Jadecky/Printer_Mods/Micron/Micron/Display Bezel Border Accent/readme.md

4.3 display bezel with minimal accent around the display border. 

Can be split and printed with an MMU, or a simple filament swap at 1.2mm.

Has built in support for optional accent logo insert.

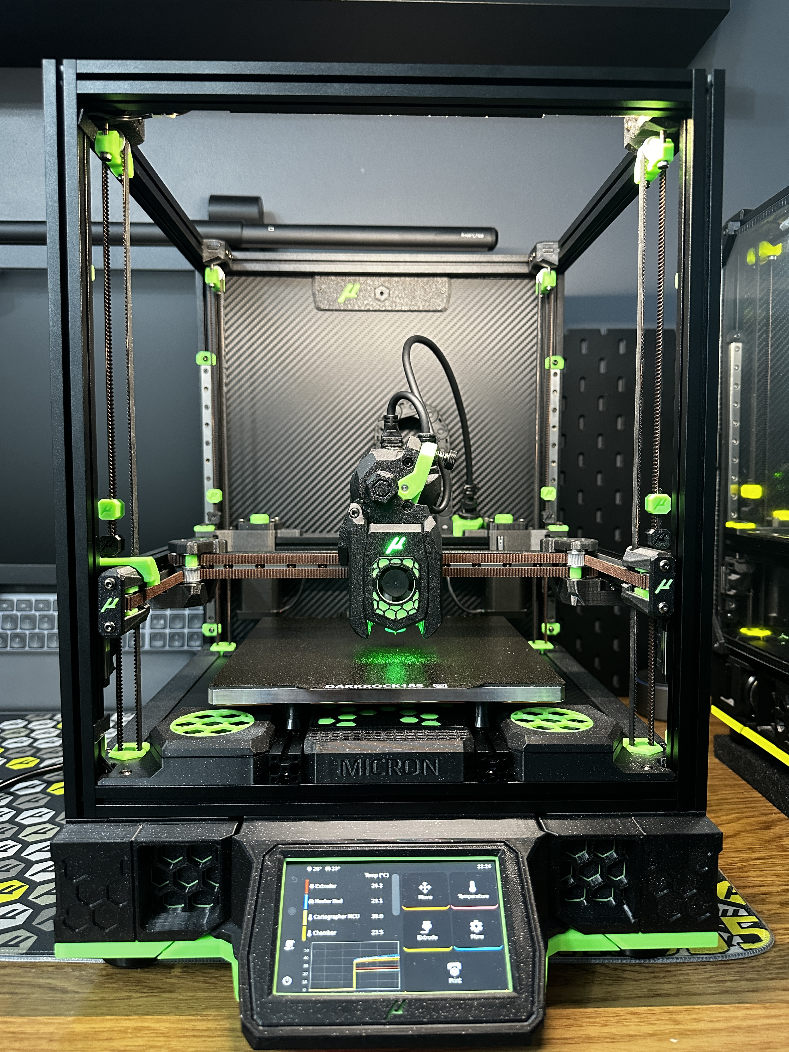
[picture p29: Micron/Micron/Display Bezel Border Accent/Images/Printed.JPG]
Printed


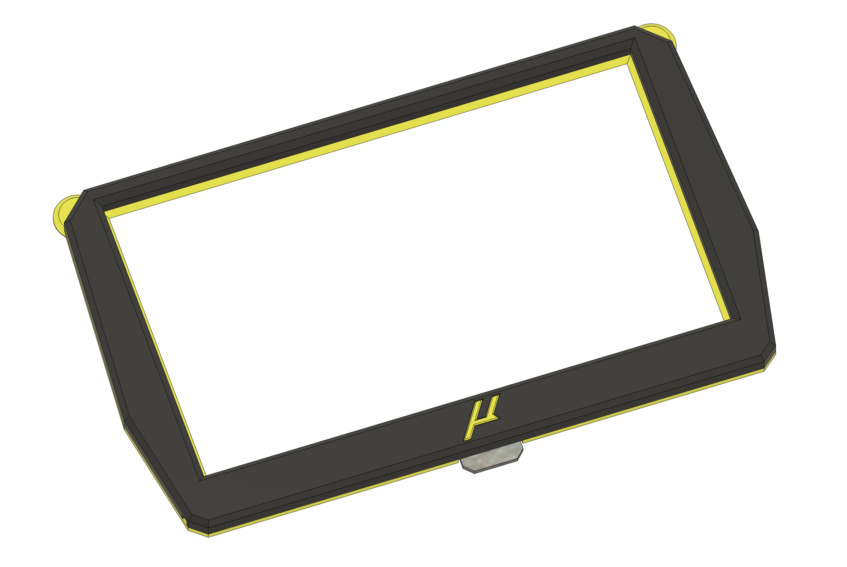
[picture p30: Micron/Micron/Display Bezel Border Accent/Images/CAD.png]
CAD Example
