Jadecky/Printer_Mods/Micron/Micron/R1 Spool Holder_Dual Colour/readme.md

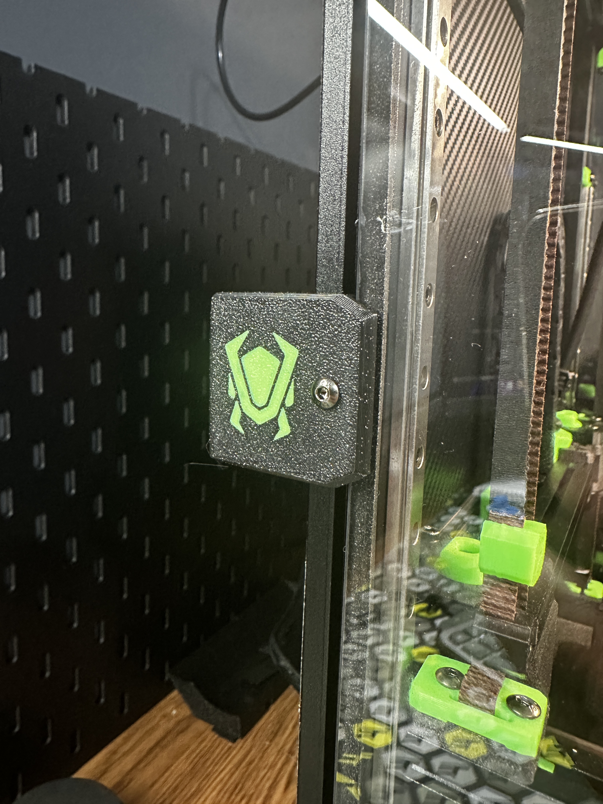
[picture p31: Micron/Micron/R1 Spool Holder_Dual Colour/Images/Printed.JPG]
Printed


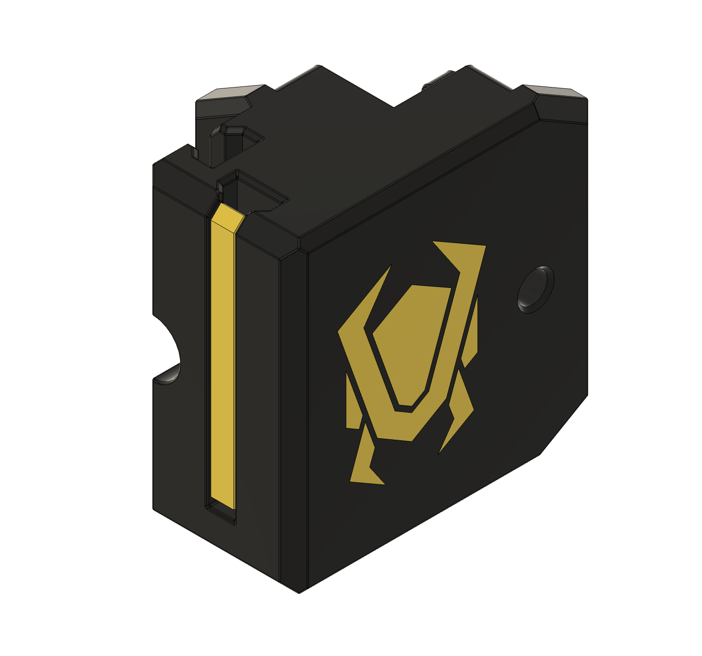
[picture p32: Micron/Micron/R1 Spool Holder_Dual Colour/Images/CAD.png]
CAD Example
