Jadecky/Printer_Mods/Micron/Micron/Stealth Fan Grills/README.md

# Stealth Fan Grills for Micron+

Slight modification to the stock **Micron+ Fan Grills**, reducing the visible accent areas for a more subtle, stealthy look.

Uses an **accent insert** for the logo — make sure you install this *before* heatsetting your grills into place.

Stealth Fan Grill Example
