Jadecky/Printer_Mods/Micron/Micron/ERCF 1515 Mount/readme.md

# ERCF 1515 Mounts for Micron+

Like the roof rack on your car — but for your printer, to carry your MMU goodness.

Designed to mount the ERCF (or other MMU setups) neatly onto the top 1515 extrusions of your Micron+.

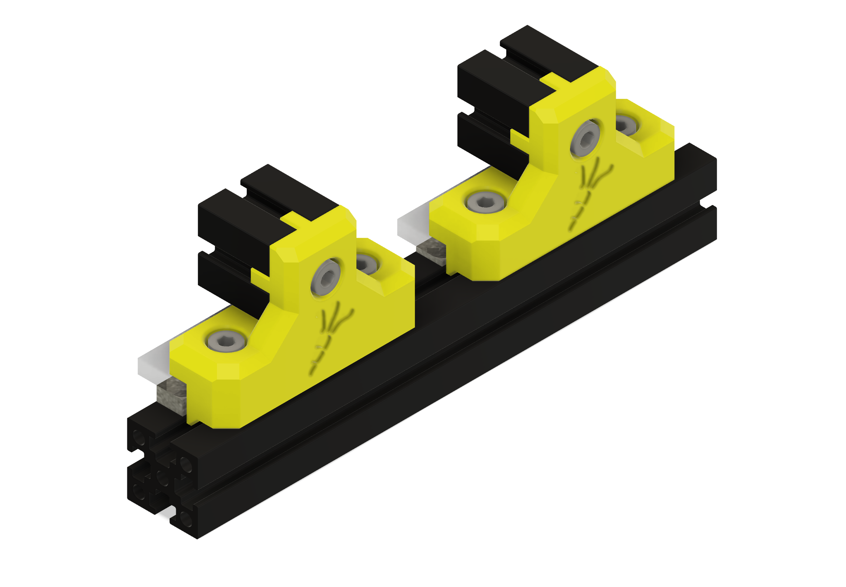
[picture p34: Micron/Micron/ERCF 1515 Mount/Images/ERCF_1515_Mounts.png]
ERCF 1515 Mount Example
