Jadecky/Printer_Mods/Micron/Micron/Micron Bed Stand Off Sleeves/README.md

# Micron Bed Stand Off Sleeves

Micron now uses stand offs to mount the bed, this makes for much easier removal and refitting. 

These standoff sleves just make them a little prettier, especially when paired with a cone washer on the bottom.

---

## 🔗 Suggested Cone / Cap head Washers

| Vendor |
|--------|
|[AliExpress](https://s.click.aliexpress.com/e/_EQEJIOK) |

|[Amazon UK](https://amzn.to/3ZXLOMW) |

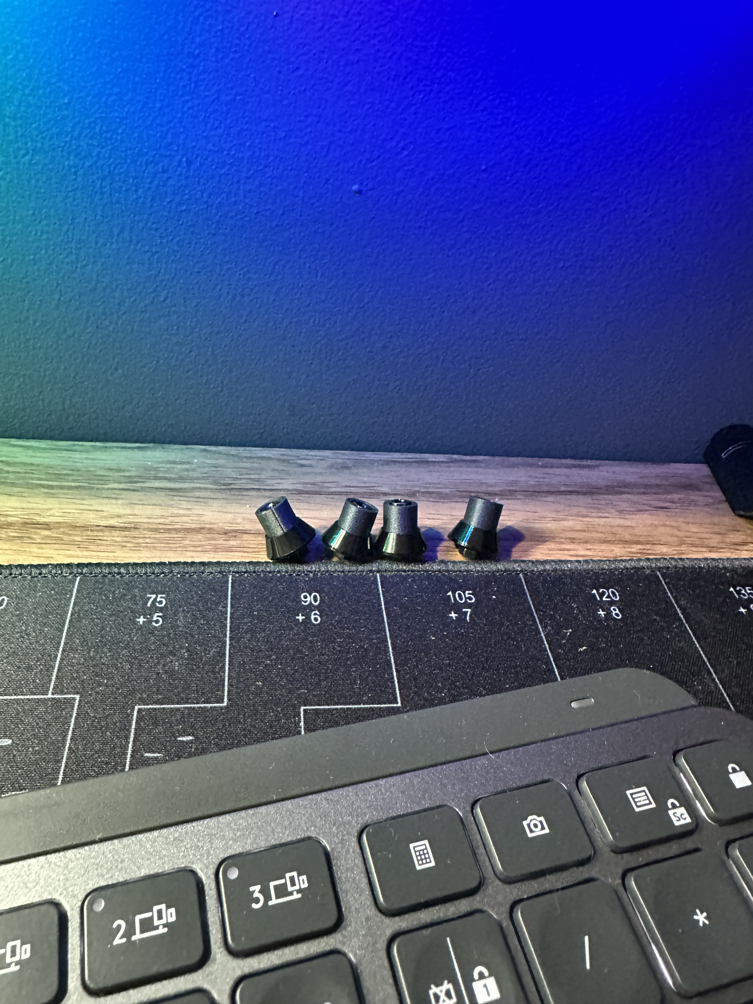
[picture p36: Micron/Micron/Micron Bed Stand Off Sleeves/Images/Standoffs.jpg]
example
