Jadecky/Printer_Mods/Micron+/WAGO_221-415_1515_Mounts/Images/Screenshot 2024-08-23 at 23.59.15.png

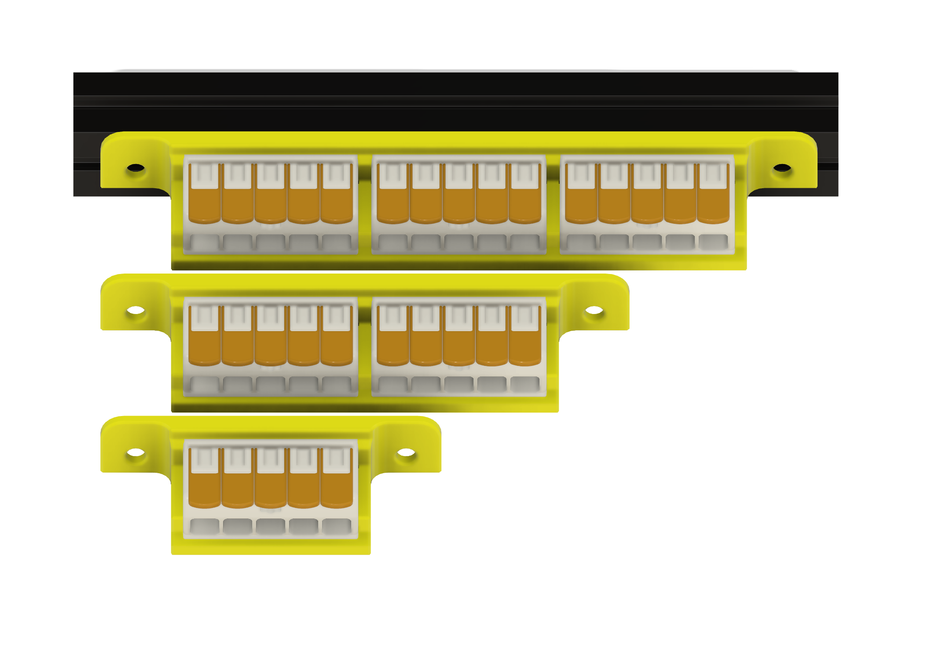
Micron+/WAGO_221-415_1515_Mounts/Images/Screenshot 2024-08-23 at 23.59.15.png
