Jadecky/Printer_Mods/Micron/Micron/AntHead_NH36 Mount/Images/Built_in_support_plug.png

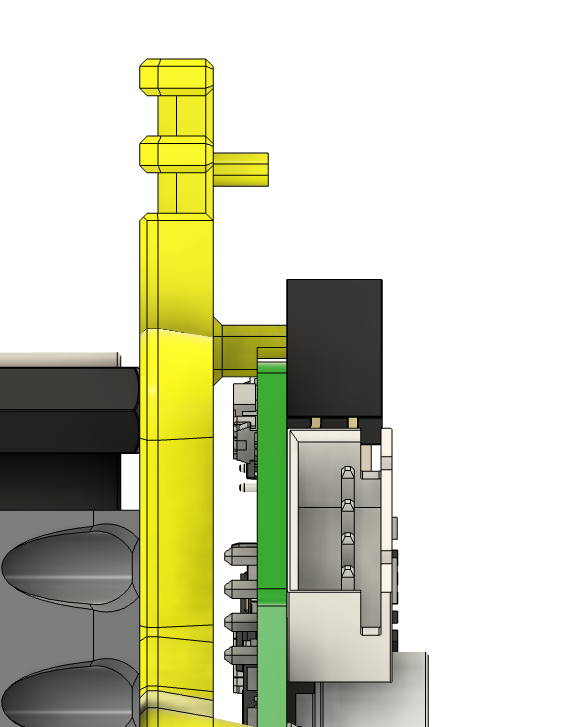
Micron/Micron/AntHead_NH36 Mount/Images/Built_in_support_plug.png
