Jadecky/Printer_Mods/Micron/Micron/Micron Z Belt Clamp/Images/Belt_path.png

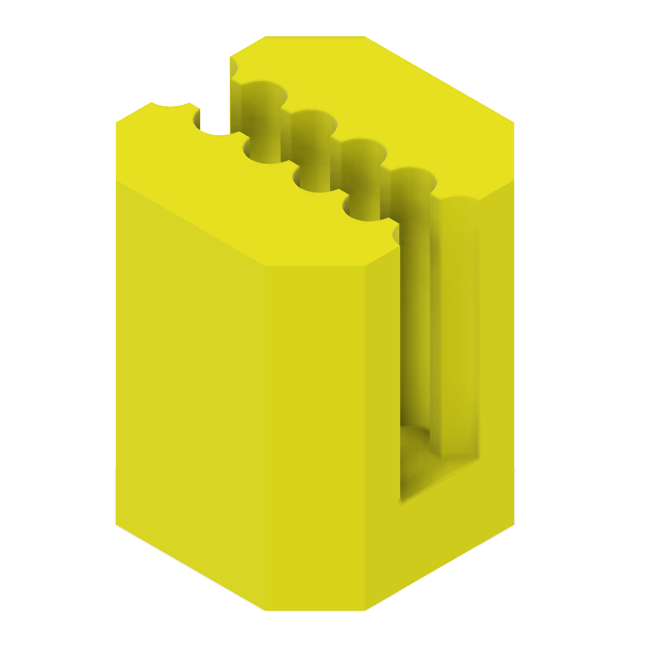
Micron/Micron/Micron Z Belt Clamp/Images/Belt_path.png
