Jadecky/Printer_Mods/Micron/Micron/Micron Z Belt Clamp/Images/IMG_4057.JPG

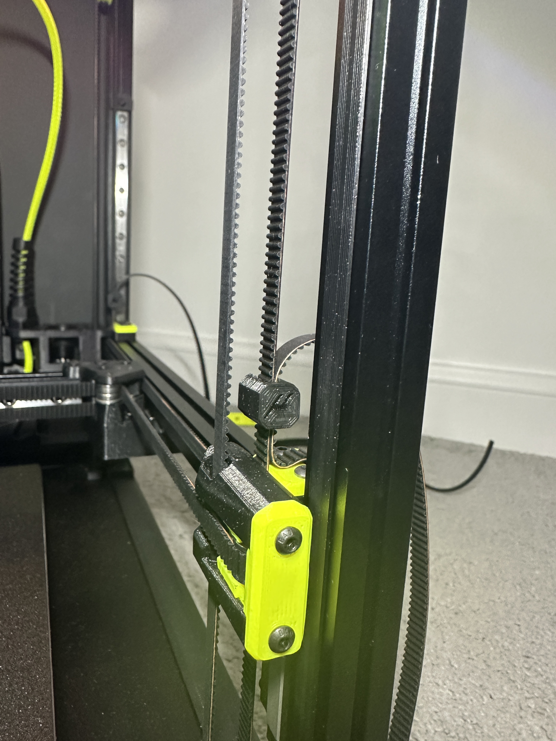
Micron/Micron/Micron Z Belt Clamp/Images/IMG_4057.JPG
