Jadecky/Printer_Mods/Micron+/Z Covers_Cable Access/[a]_Z_Belt_Cover_Cable_b_x2.stl

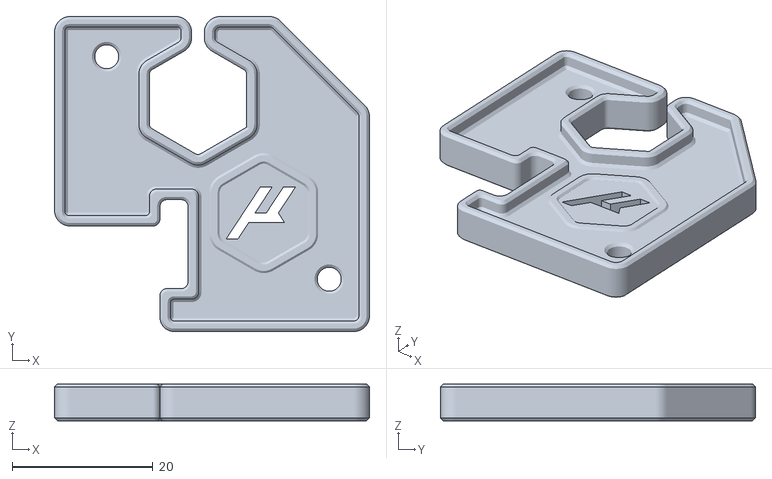
[picture p58: CAD file, 2023-08-23]
Micron+/Z Covers_Cable Access/[a]_Z_Belt_Cover_Cable_b_x2.stl
44.8 x 44.8 x 5.25
