Jadecky/Printer_Mods/Micron+/Z Covers_Cable Access/CAD/Z Drive Belt Cover_Cable_Access.step

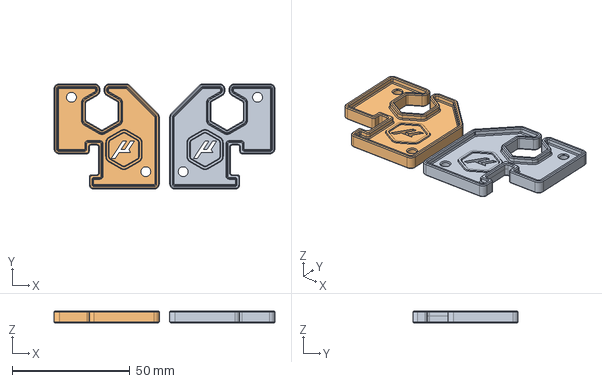
[picture p59: CAD file, 2023-08-23]
Micron+/Z Covers_Cable Access/CAD/Z Drive Belt Cover_Cable_Access.step
94.0 x 44.8 x 5.25 mm
