Jadecky/Printer_Mods/Micron/Micron/AntHead_NH36 Mount/STLs/18mm Standoff/[a]_Spacer_R_18mmStandoff_x1.stl

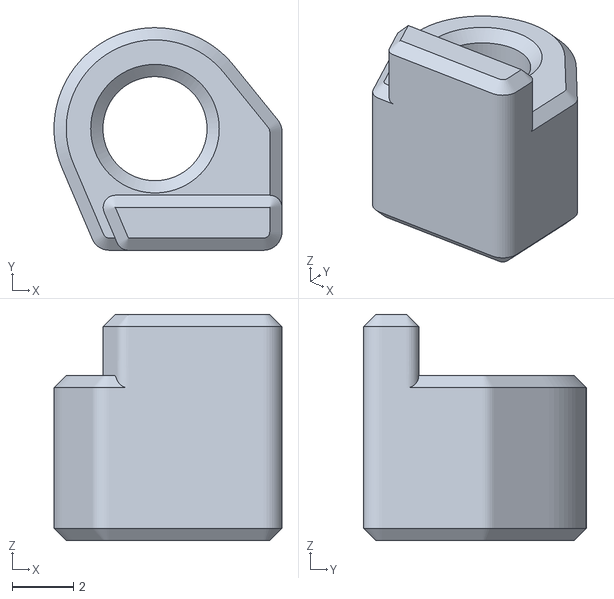
[picture p60: CAD file, 2025-10-04]
Micron/Micron/AntHead_NH36 Mount/STLs/18mm Standoff/[a]_Spacer_R_18mmStandoff_x1.stl
7.45 x 7.27 x 7.40
