Jadecky/Printer_Mods/Micron/Micron/AntHead_NH36 Mount/STLs/20mm Standoff/[a]_Spacer_L_20mm_Standoff_x1.stl

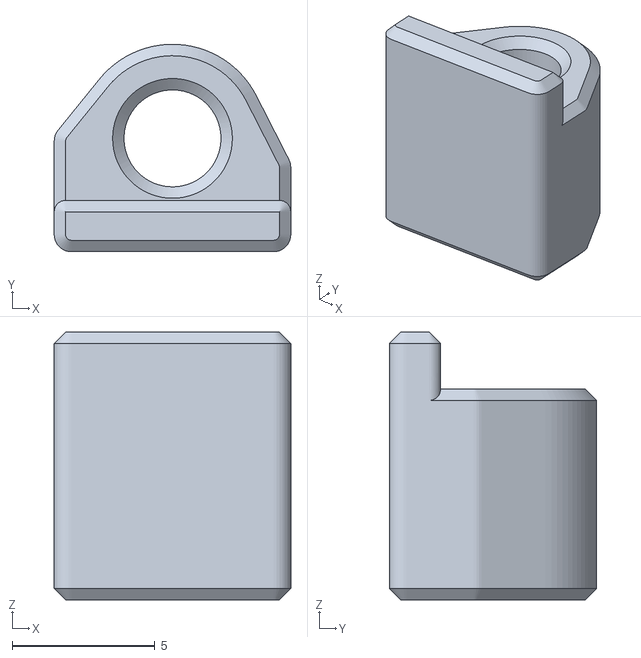
[picture p61: CAD file, 2025-10-04]
Micron/Micron/AntHead_NH36 Mount/STLs/20mm Standoff/[a]_Spacer_L_20mm_Standoff_x1.stl
8.30 x 7.27 x 9.40
