Jadecky/Printer_Mods/Micron/Micron/AntHead_NH36 Mount/STLs/[a]_NH36_Mount_no_tabs_x1.stl

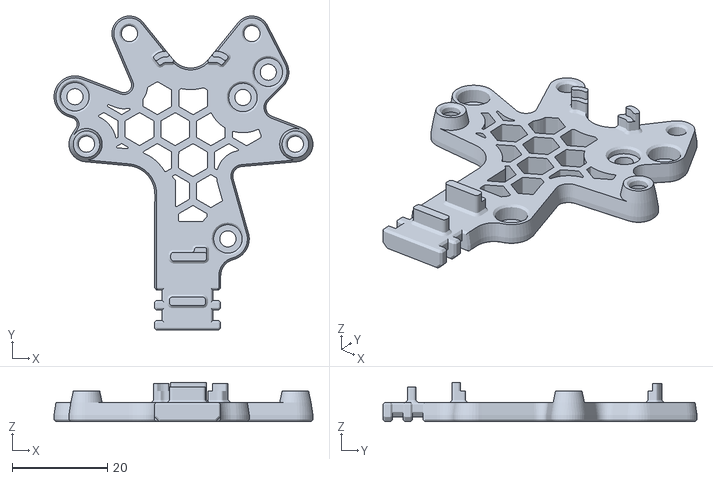
[picture p62: CAD file, 2025-10-04]
Micron/Micron/AntHead_NH36 Mount/STLs/[a]_NH36_Mount_no_tabs_x1.stl
54.4 x 65.9 x 8.20
