Jadecky/Printer_Mods/Micron/Micron/Display Bezel Border Accent/CAD/Bezel_accent_border.step

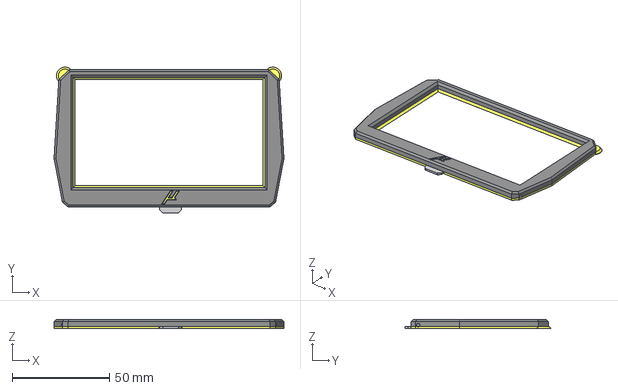
[picture p63: CAD file, 2025-07-15]
Micron/Micron/Display Bezel Border Accent/CAD/Bezel_accent_border.step
118.3 x 75.0 x 4.80 mm
Bezel_x1
[a]_Bezel_insert_x1
