Jadecky/Printer_Mods/Micron/Micron/Display Bezel Border Accent/STLs/[a]_Bezel_logo_insert_x1.stl

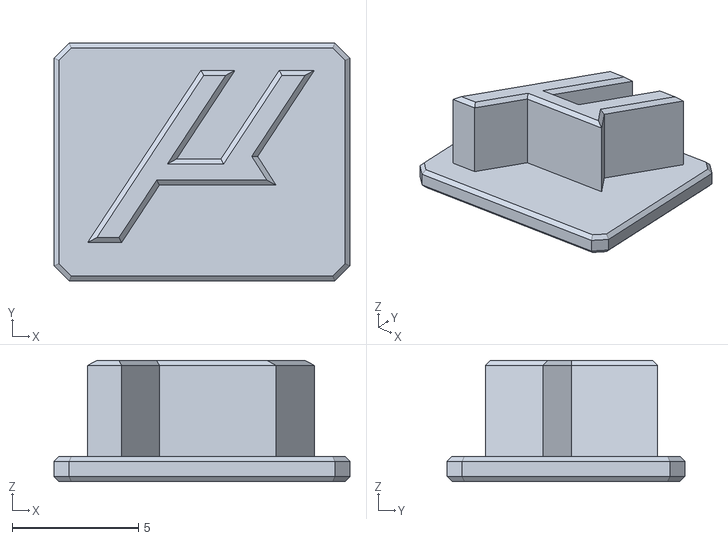
[picture p64: CAD file, 2025-07-15]
Micron/Micron/Display Bezel Border Accent/STLs/[a]_Bezel_logo_insert_x1.stl
11.7 x 9.42 x 4.80
