Jadecky/Printer_Mods/Micron/Micron/ERCF 1515 Mount/CAD/ERCF_1515_Mount.step

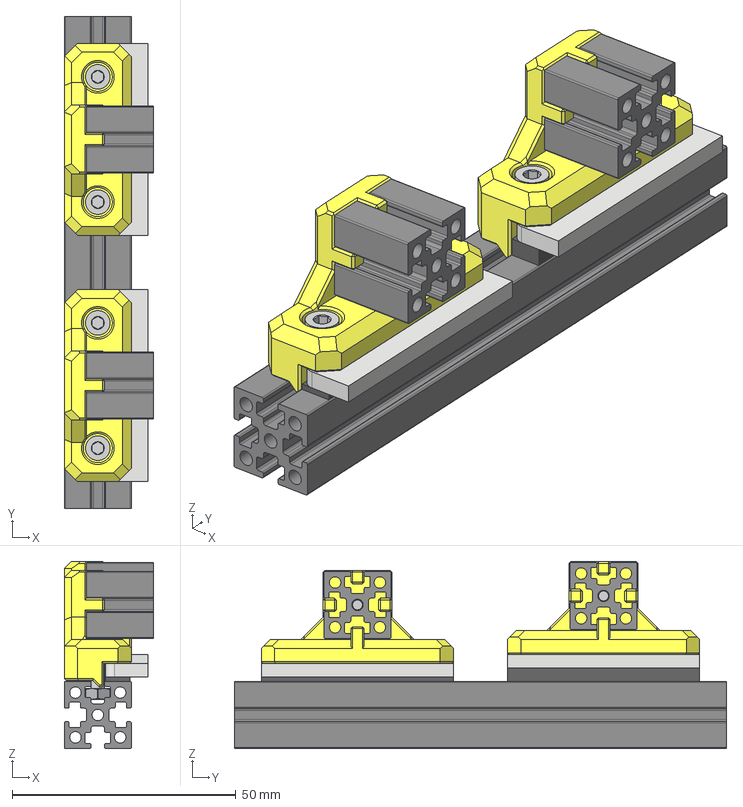
[picture p65: CAD file, 2024-08-23]
Micron/Micron/ERCF 1515 Mount/CAD/ERCF_1515_Mount.step
20.0 x 110.0 x 41.8 mm
ERCF_1515_Mount_1mm_Foam_x4
ERCF_1515_Mount_3mm_Foam_x4
M3x10 SHCS
M3x10 SHCS_1
M3x10 SHCS_2
M3x10 SHCS_3
M3x10 SHCS_4
M3x10 SHCS_5
1515 Extrusion
3mm_Panel (1)
1mm_Foam
3mm_Foam (1)
M3_Hexnut
M3_Hexnut_1
M3_Hexnut_2
M3_Hexnut_3
