Jadecky/Printer_Mods/Micron/Micron/ERCF 1515 Mount/STLs/ERCF_1515_Mount_3mm_Foam_x4.stl

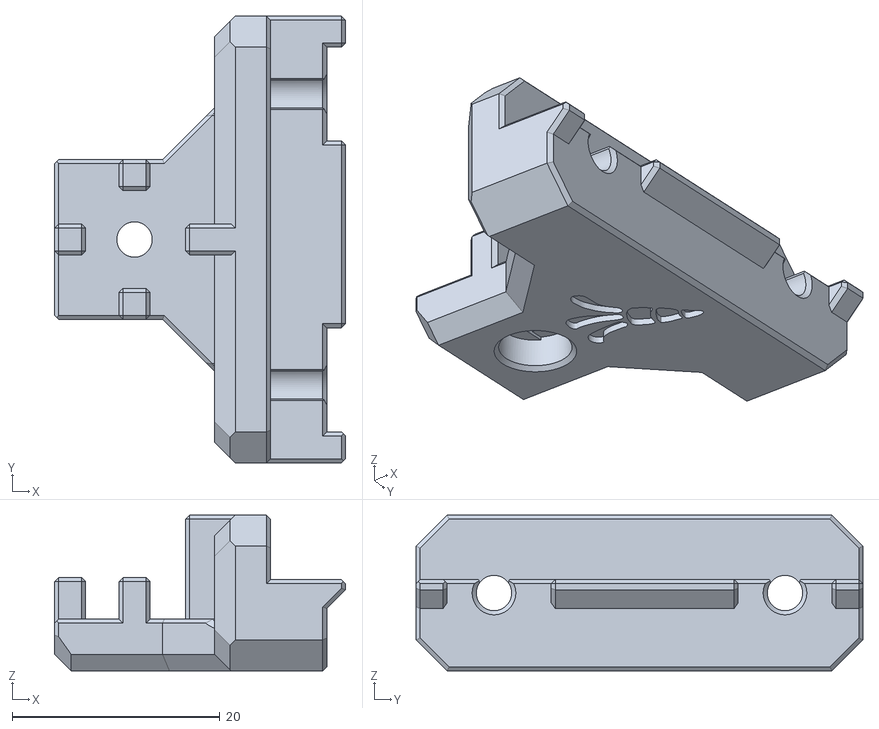
[picture p66: CAD file, 2024-08-23]
Micron/Micron/ERCF 1515 Mount/STLs/ERCF_1515_Mount_3mm_Foam_x4.stl
28.0 x 43.0 x 15.0
