Jadecky/Printer_Mods/Micron/Micron/Matchstick Mounts/STLs/1515_Matchstick_Clip_45.stl

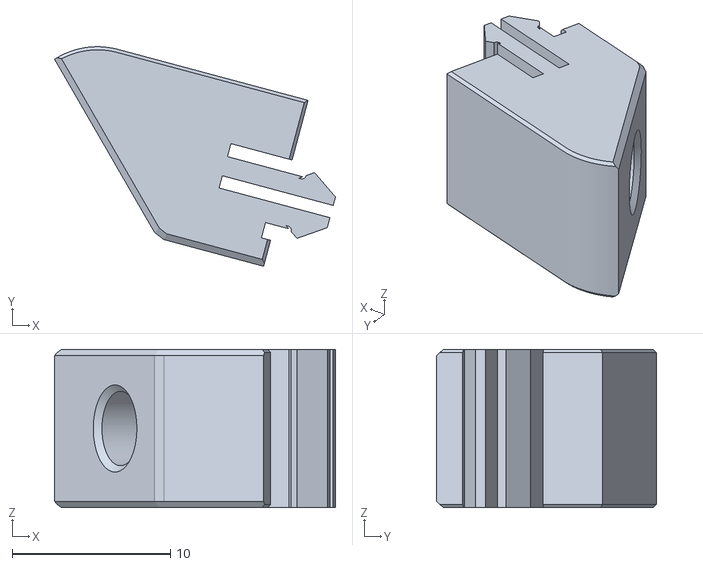
[picture p67: CAD file, 2023-12-18]
Micron/Micron/Matchstick Mounts/STLs/1515_Matchstick_Clip_45.stl
17.7 x 13.9 x 10.0
