Jadecky/Printer_Mods/Micron/Micron/Micron Bed Stand Off Sleeves/CAD/Micron_Bed_Stand_Offs.step

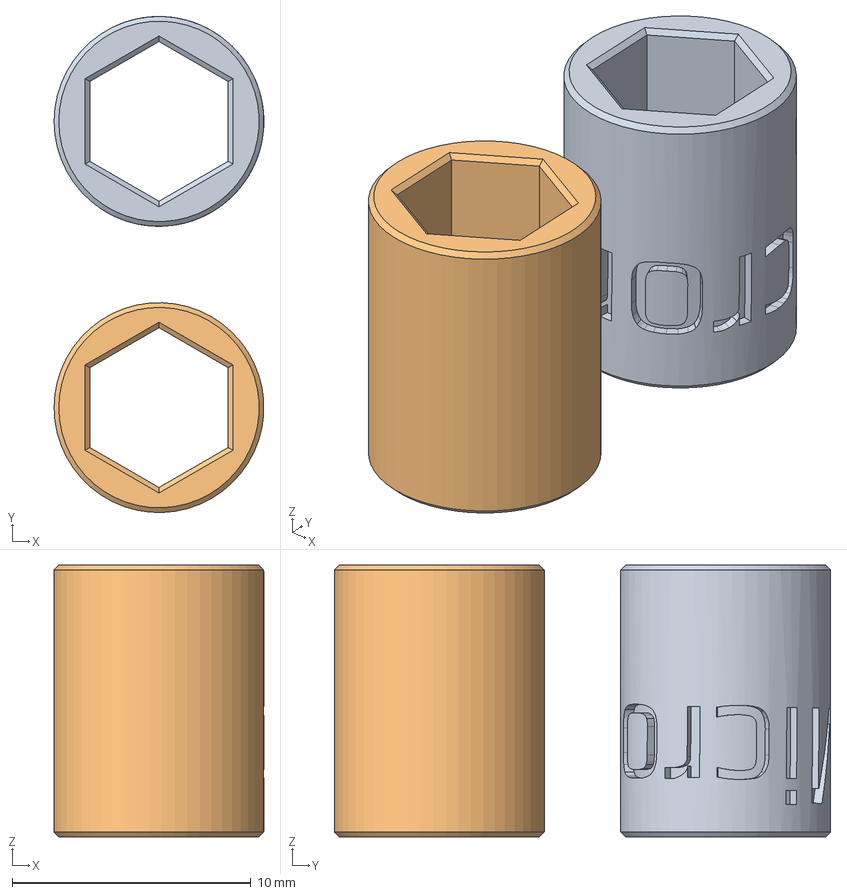
[picture p68: CAD file, 2024-08-17]
Micron/Micron/Micron Bed Stand Off Sleeves/CAD/Micron_Bed_Stand_Offs.step
8.80 x 20.8 x 11.4 mm
Bed Standoff Sleeve_Micron
Bed Standoff Sleeve
