Jadecky/Printer_Mods/Micron/Micron/Micron Bed Stand Off Sleeves/STLs/[a]_Micron_Bed_Stand_Off_Micron_Text.stl

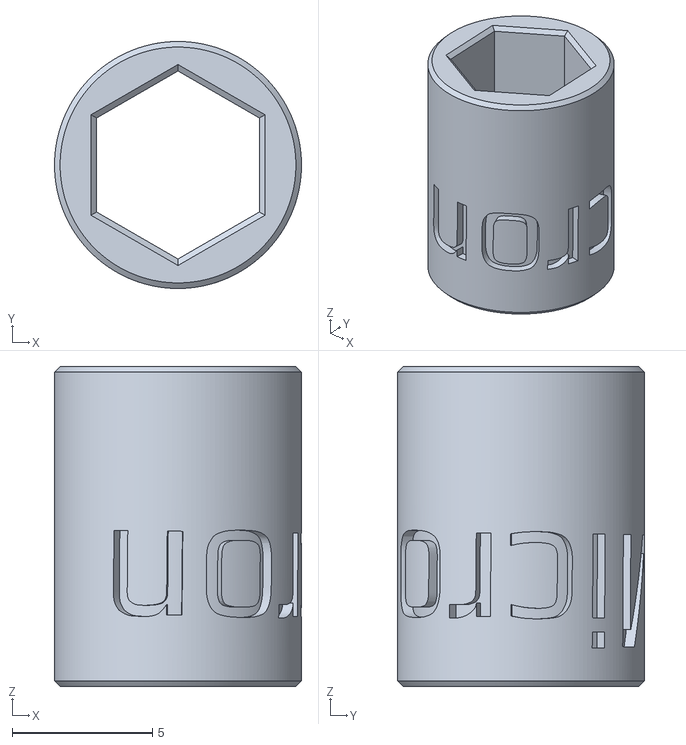
[picture p69: CAD file, 2024-08-17]
Micron/Micron/Micron Bed Stand Off Sleeves/STLs/[a]_Micron_Bed_Stand_Off_Micron_Text.stl
8.80 x 8.80 x 11.4
