Jadecky/Printer_Mods/Micron/Micron/Micron Z Belt Clamp/CAD/Z_Belt_Clip_Micron.step

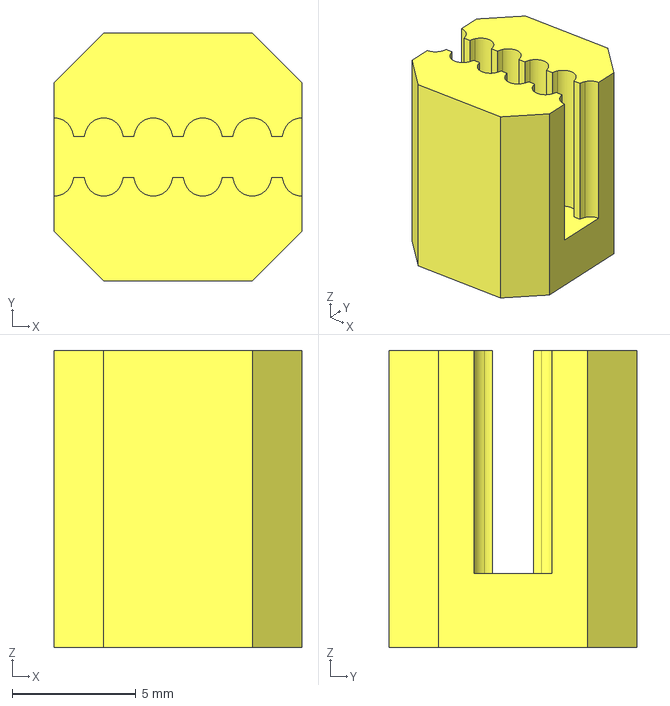
[picture p70: CAD file, 2023-08-28]
Micron/Micron/Micron Z Belt Clamp/CAD/Z_Belt_Clip_Micron.step
10.0 x 10.0 x 12.0 mm
