Jadecky/Printer_Mods/Micron/Micron/Micron_NEMA17/STLs/[a]_B_Drive_Top_Bearing_Mount_x1.stl

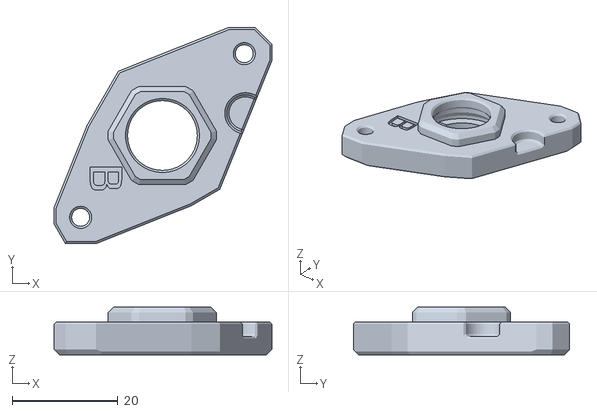
[picture p72: CAD file, 2025-10-28]
Micron/Micron/Micron_NEMA17/STLs/[a]_B_Drive_Top_Bearing_Mount_x1.stl
41.3 x 41.0 x 9.00
