Jadecky/Printer_Mods/Micron/Micron/R1 Spool Holder_Dual Colour/CAD/R1_SpoolHolder_DualColour.step

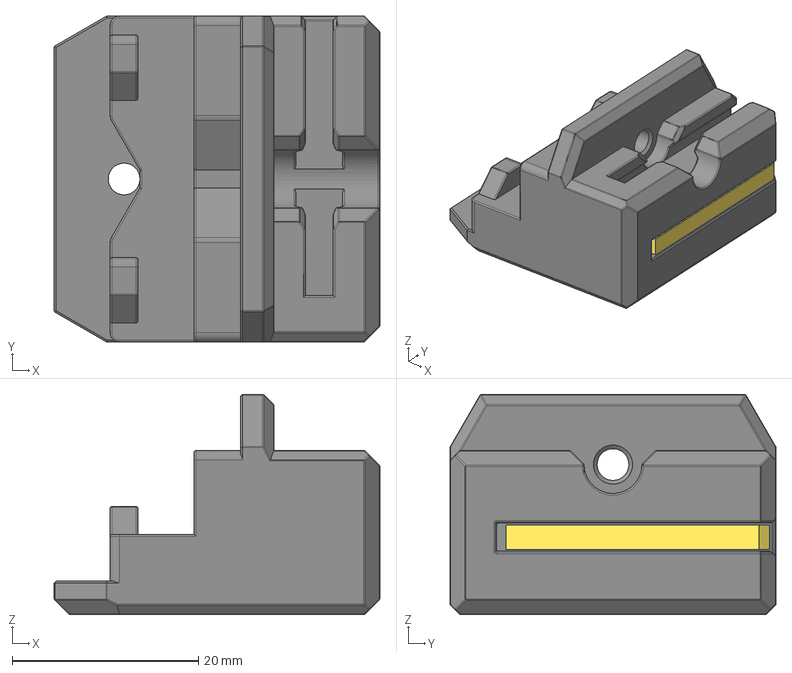
[picture p74: CAD file, 2025-07-15]
Micron/Micron/R1 Spool Holder_Dual Colour/CAD/R1_SpoolHolder_DualColour.step
35.0 x 35.0 x 23.6 mm
