Jadecky/Printer_Mods/Micron/Micron/Skirt Accent Single Piece/CAD/Center_Skirt_Accent v2.step

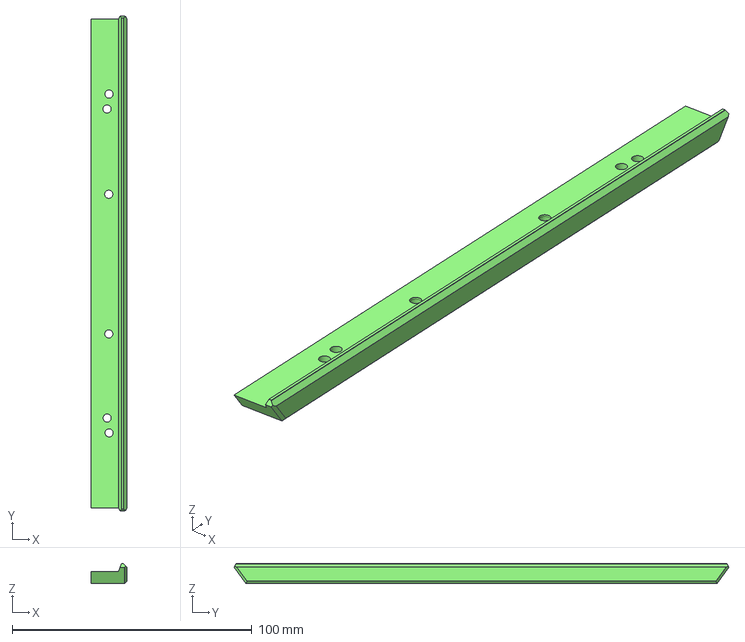
[picture p75: CAD file, 2025-06-29]
Micron/Micron/Skirt Accent Single Piece/CAD/Center_Skirt_Accent v2.step
15.0 x 206.5 x 8.40 mm
