Jadecky/Printer_Mods/Micron/Micron/Stealth Fan Grills/CAD/Stealth_Fan_Grill.step

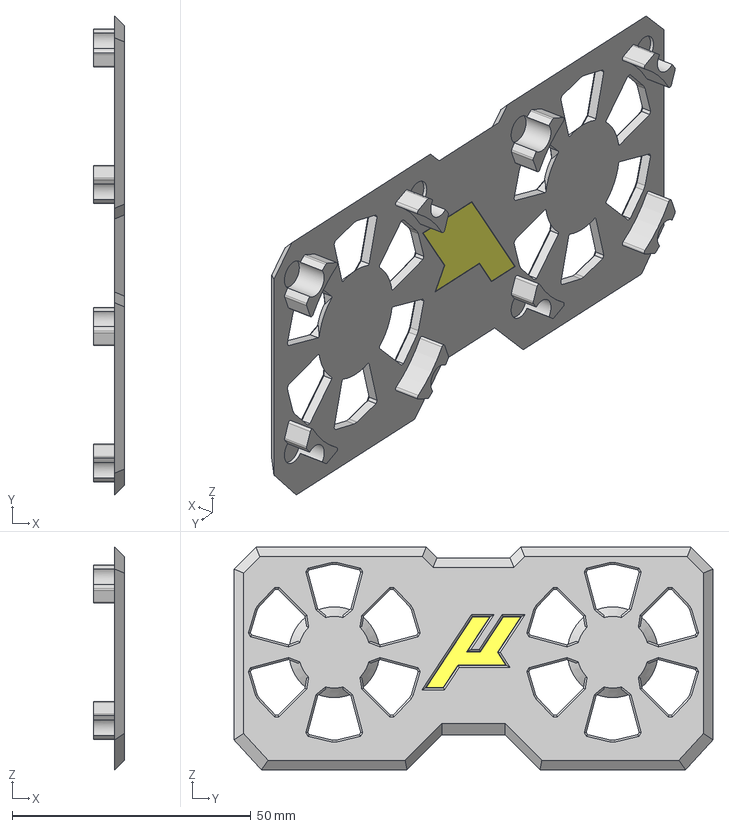
[picture p76: CAD file, 2025-06-29]
Micron/Micron/Stealth Fan Grills/CAD/Stealth_Fan_Grill.step
6.40 x 100.3 x 46.6 mm
[a]_Fan_Grill_Logo_Insert_x2
Fan_Grill_x2
[a]_Fan_Grill_Logo_Insert_x2 (1)
