Jadecky/Printer_Mods/Micron/Micron/Stealth Fan Grills/STLs/[a]_Fan_Grill_Accent_Insert_x2.stl

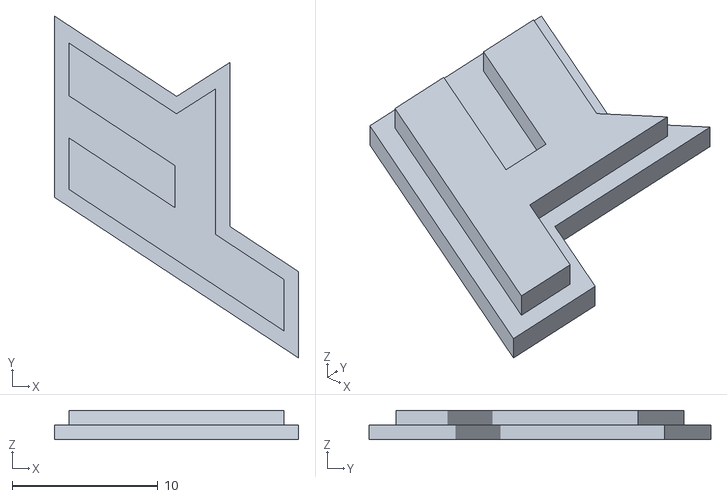
[picture p77: CAD file, 2025-06-29]
Micron/Micron/Stealth Fan Grills/STLs/[a]_Fan_Grill_Accent_Insert_x2.stl
16.7 x 23.5 x 2.00
