Jadecky/Printer_Mods/Misc Items/Bed Aux Umbilical/CAD/Bed_Aux_Umbiical_PCB.step

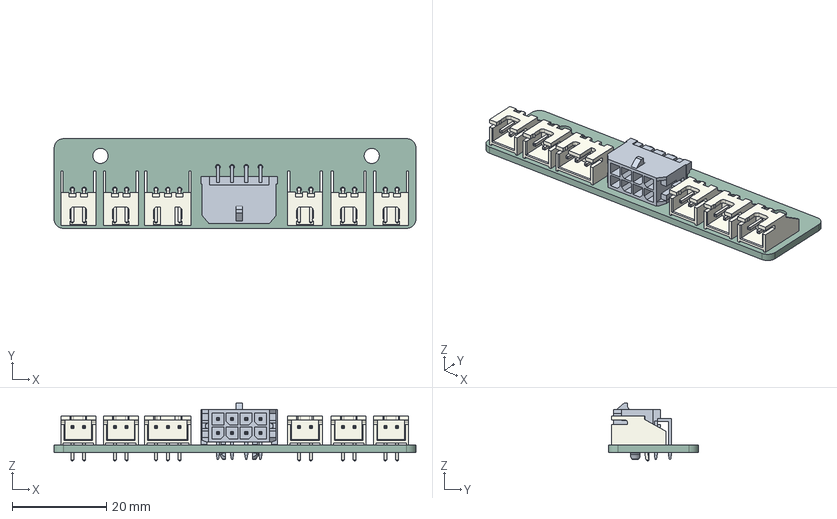
[picture p78: CAD file, 2025-11-23]
Misc Items/Bed Aux Umbilical/CAD/Bed_Aux_Umbiical_PCB.step
76.6 x 19.0 x 12.2 mm
JST_XH_S2B-XH-A-1_1x02_P2.50mm_Horizontal x 5
JST_XH_S3B-XH-A-1_1x03_P2.50mm_Horizontal
Bed_Aux_Umbiical_PCB_PCB
