Jadecky/Printer_Mods/Misc Items/Bed Aux Umbilical/STLs/Bed_Aux_Umbilical_Mount.stl

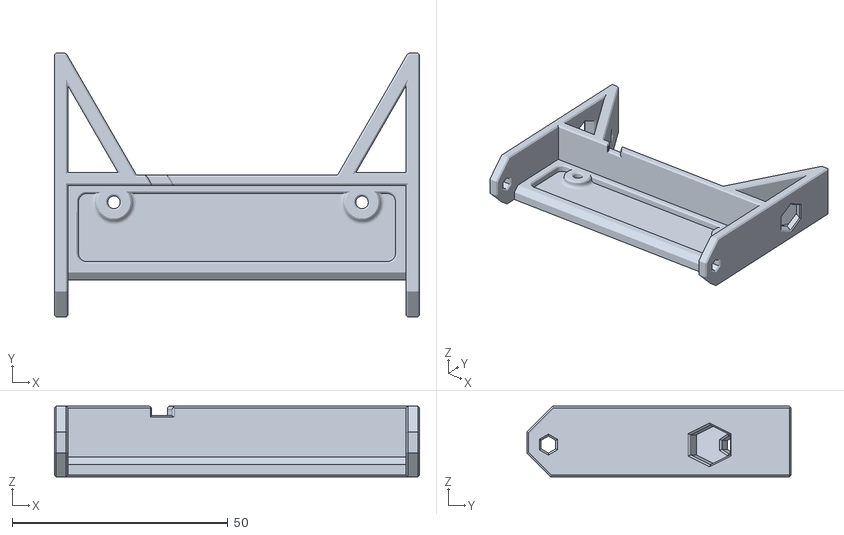
[picture p79: CAD file, 2025-11-23]
Misc Items/Bed Aux Umbilical/STLs/Bed_Aux_Umbilical_Mount.stl
84.5 x 61.2 x 16.4
