Jadecky/Printer_Mods/Misc Items/F623 Bearing Repacker/CAD/F623_Bearing_Packer.step

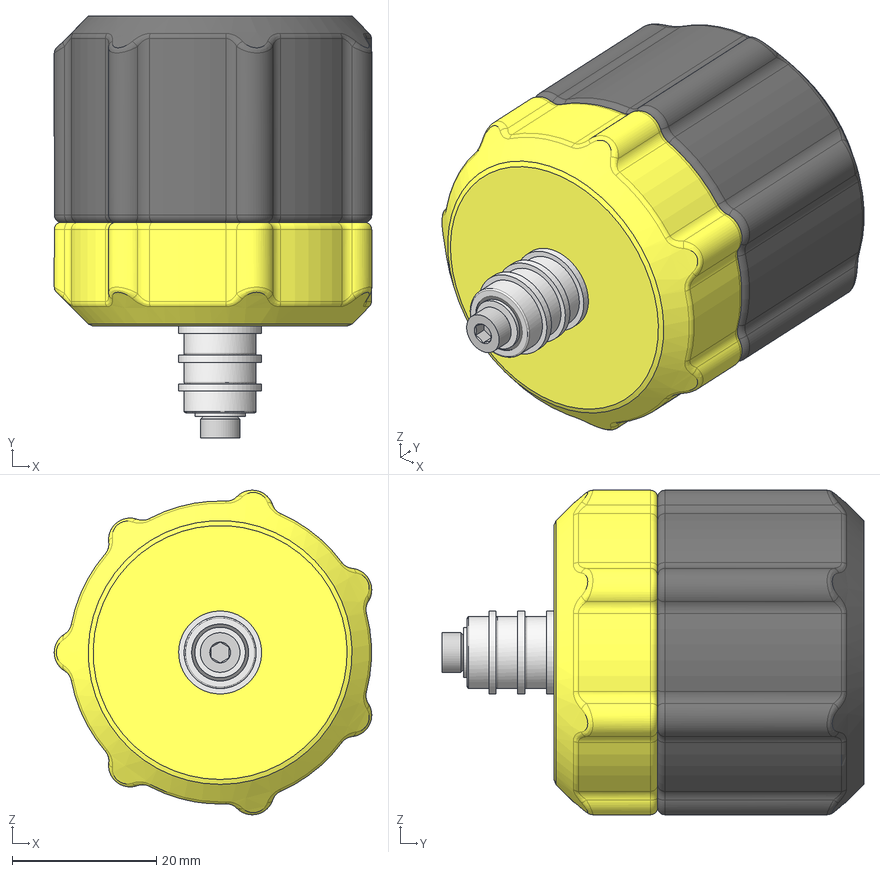
[picture p80: CAD file, 2024-10-31]
Misc Items/F623 Bearing Repacker/CAD/F623_Bearing_Packer.step
44.0 x 58.5 x 45.0 mm
Bottem
Top
F623 Bearing_1
F623 Bearing_2
M3 Shim Washer
(Unsaved)
M3x30 SHCS
