Jadecky/Printer_Mods/Misc Items/F623 Bearing Repacker/STLs/Top_x1.stl

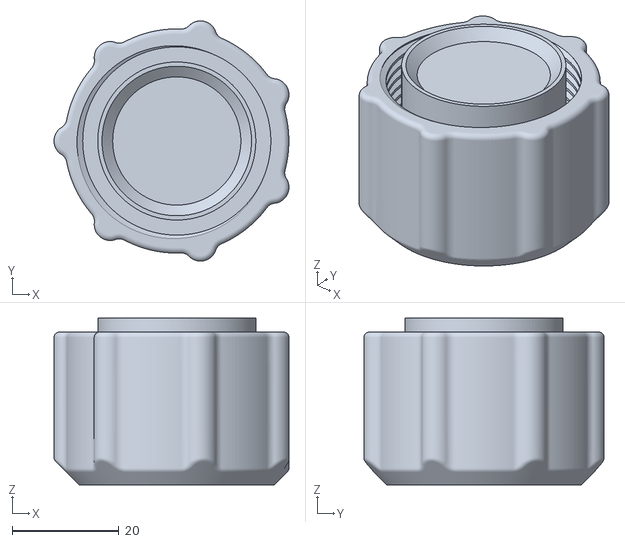
[picture p81: CAD file, 2024-10-31]
Misc Items/F623 Bearing Repacker/STLs/Top_x1.stl
44.0 x 45.0 x 31.2
