Jadecky/Printer_Mods/Misc Items/Micron Really Useful Tool/CAD/Micron Really Useful Tool.step

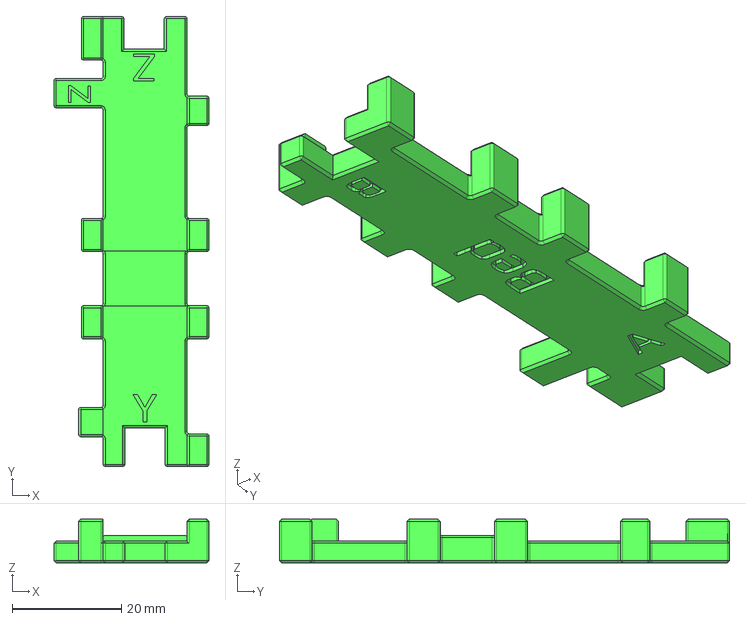
[picture p82: CAD file, 2025-07-20]
Misc Items/Micron Really Useful Tool/CAD/Micron Really Useful Tool.step
28.4 x 82.5 x 8.00 mm
