Jadecky/Printer_Mods/V0/V0_Lower_DIN_Rail_Mount/STLs/[a]_V0_lower_DIN_rail_mount_x2.stl

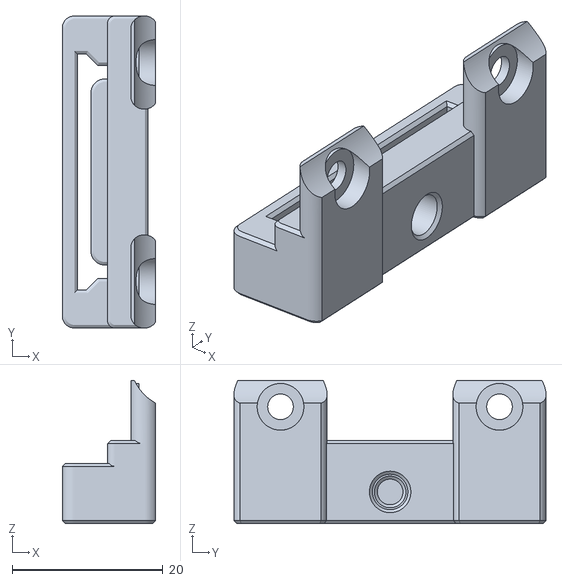
[picture p83: CAD file, 2025-02-17]
V0/V0_Lower_DIN_Rail_Mount/STLs/[a]_V0_lower_DIN_rail_mount_x2.stl
12.4 x 41.4 x 19.0
