Jadecky/Printer_Mods/V0/V0_Rear DIN Rail Mount/CAD/V0_Rear_DIN_Rail_Mount.step

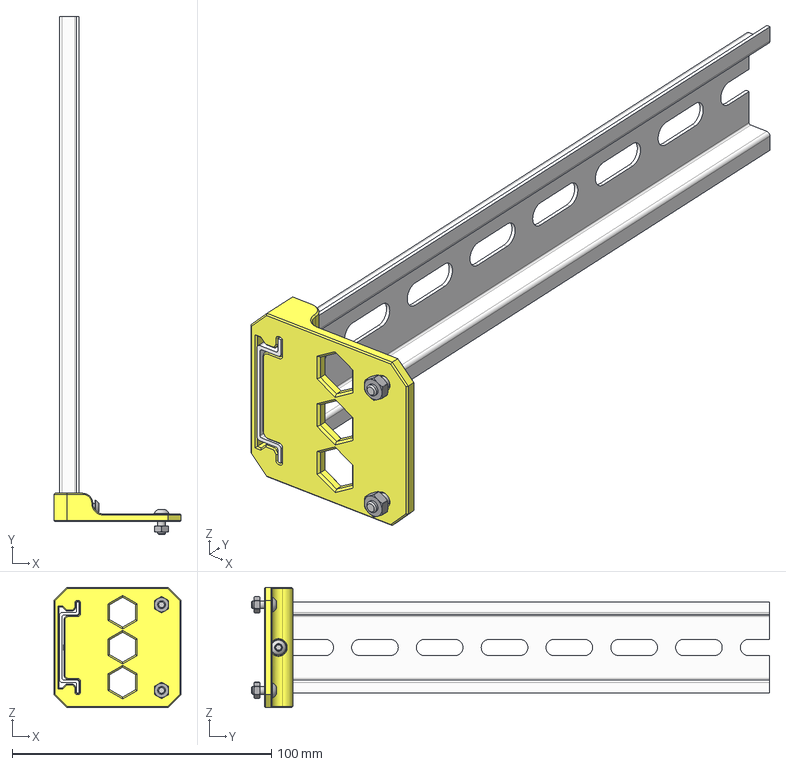
[picture p84: CAD file, 2025-02-17]
V0/V0_Rear DIN Rail Mount/CAD/V0_Rear_DIN_Rail_Mount.step
49.0 x 200.0 x 46.3 mm
Printed Mount
(Unsaved)
DIN3 Rail
M3x12 BHCS
M3x10 BHCS x 2
M3_Hexnut x 2
