Jadecky/Printer_Mods/V0/V0_Rear DIN Rail Mount/STLs/[a]_V0_printed_rear_din_rail_mount_x2.stl

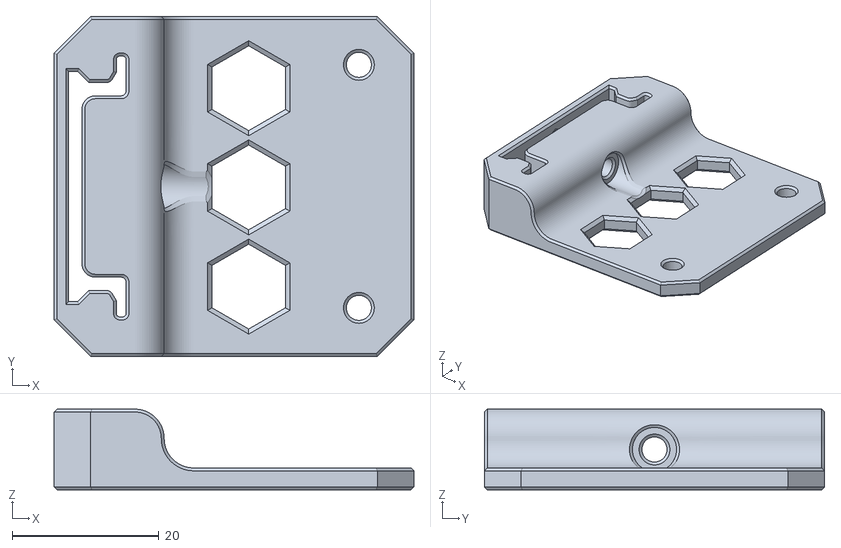
[picture p85: CAD file, 2025-02-17]
V0/V0_Rear DIN Rail Mount/STLs/[a]_V0_printed_rear_din_rail_mount_x2.stl
49.0 x 46.3 x 11.0
