Jadecky/Printer_Mods/V0/V0_UHP_Mounts/STLs/[a]_Voron_V0_UHP_Mount_x2.stl

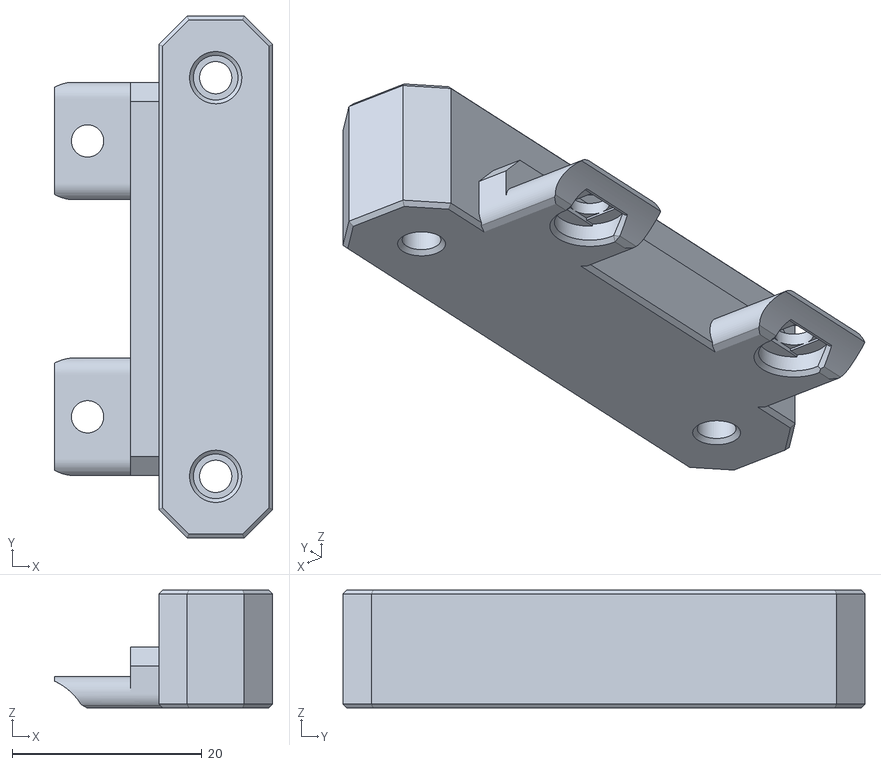
[picture p86: CAD file, 2025-02-17]
V0/V0_UHP_Mounts/STLs/[a]_Voron_V0_UHP_Mount_x2.stl
23.0 x 55.0 x 12.4
