Jadecky/Printer_Mods/Micron+/KGLM Hex Z Joint/[a]_Z_Joint_Hex__No_Logo_x4.stl

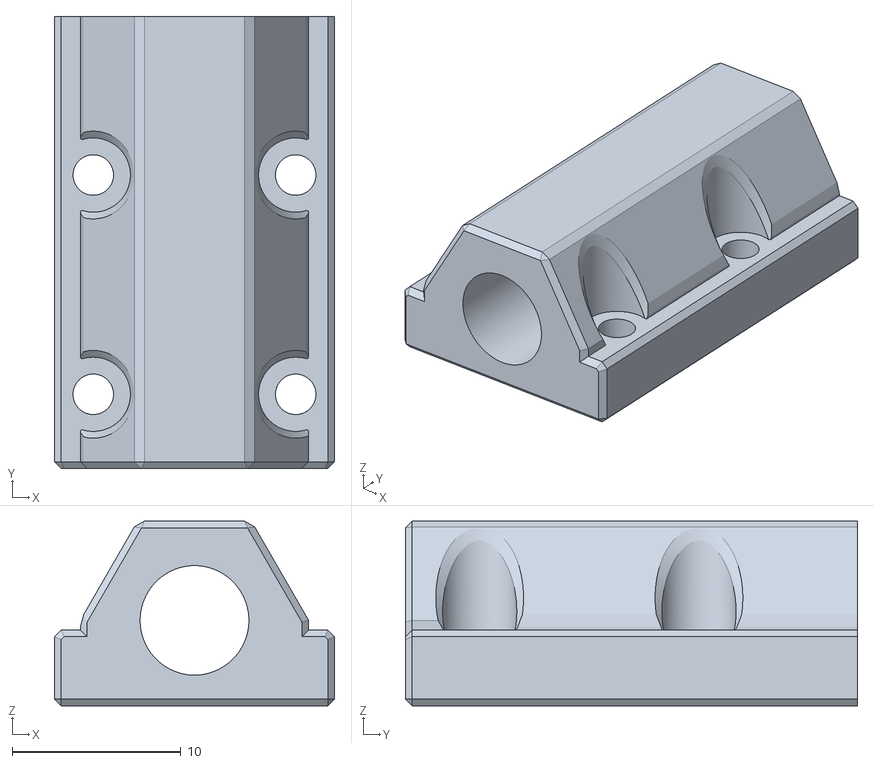
[picture p87: CAD file, 2023-08-28]
Micron+/KGLM Hex Z Joint/[a]_Z_Joint_Hex__No_Logo_x4.stl
16.6 x 26.8 x 11.0
