Jadecky/Printer_Mods/Micron+/MDC/STLs/Heatset Version/Drill Guides/Drill_Guide_Handle.stl

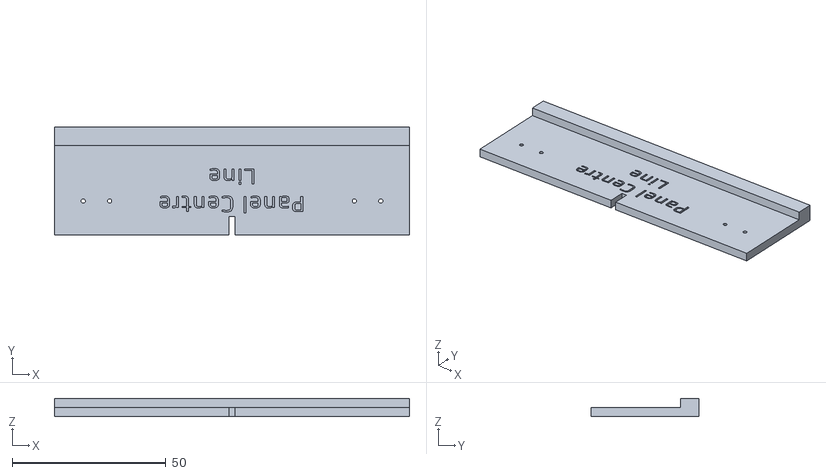
[picture p88: CAD file, 2023-09-10]
Micron+/MDC/STLs/Heatset Version/Drill Guides/Drill_Guide_Handle.stl
115.3 x 35.0 x 6.00
