Jadecky/Printer_Mods/Micron+/MDC/STLs/Heatset Version/Top_Left_Door_Corner.stl

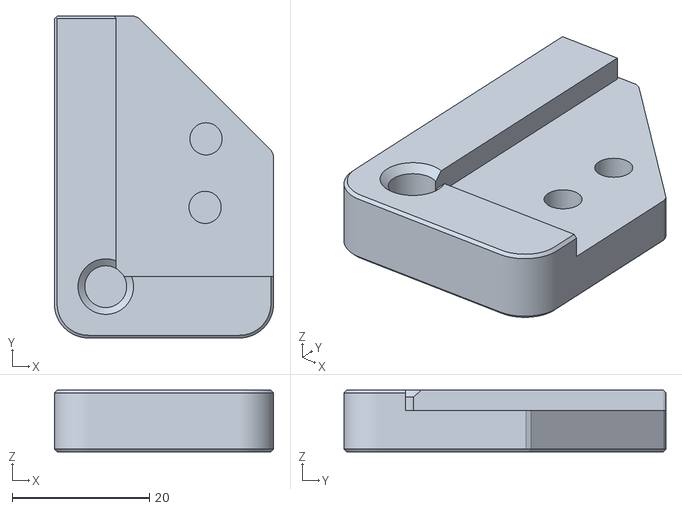
[picture p89: CAD file, 2023-09-10]
Micron+/MDC/STLs/Heatset Version/Top_Left_Door_Corner.stl
32.0 x 47.0 x 9.00
