Jadecky/Printer_Mods/Micron+/MDC/STLs/VHB Tape Version/VHB_Top_Hinge_Door_Mount_MMU.stl

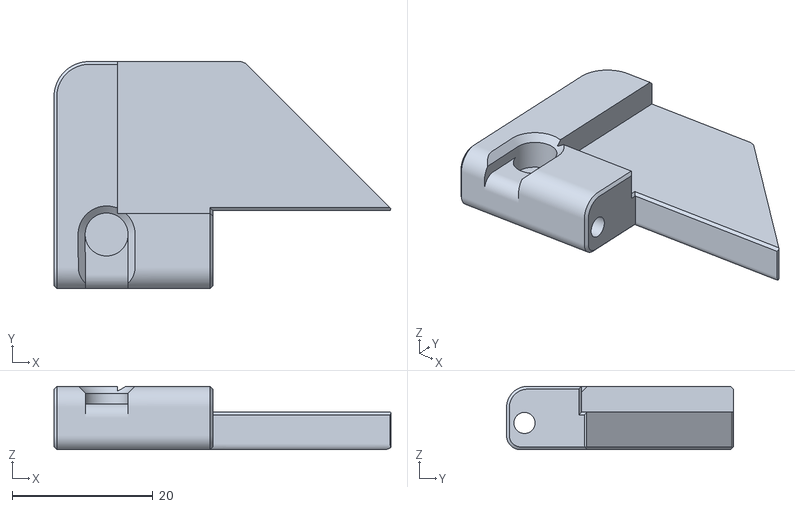
[picture p90: CAD file, 2023-09-10]
Micron+/MDC/STLs/VHB Tape Version/VHB_Top_Hinge_Door_Mount_MMU.stl
47.9 x 32.2 x 9.00
