Jadecky/Printer_Mods/Micron+/Smol Hex Skirts/STLs/Front - 3.5 Touchscreen/Smol_Hex_Front_Skirt_35_Touch_Screen_Bracket_R.stl

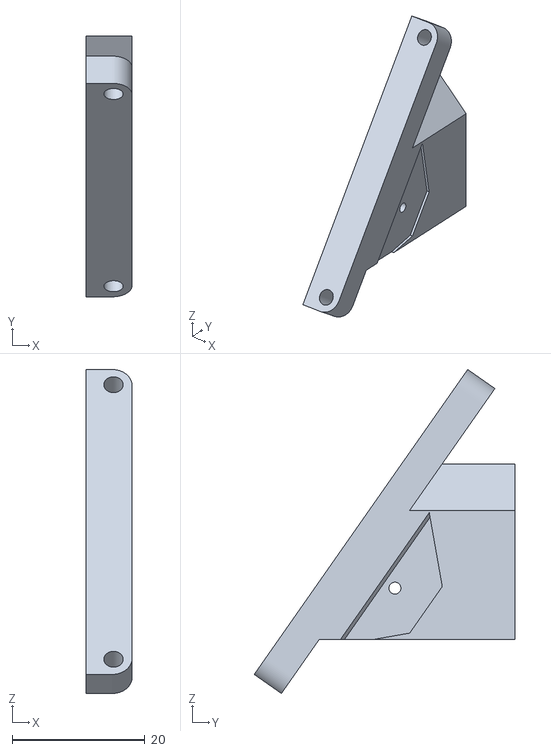
[picture p91: CAD file, 2023-08-23]
Micron+/Smol Hex Skirts/STLs/Front - 3.5 Touchscreen/Smol_Hex_Front_Skirt_35_Touch_Screen_Bracket_R.stl
6.97 x 39.2 x 48.7
