Jadecky/Printer_Mods/Micron+/Smol Hex Skirts/STLs/Front - 4.3 Touchscreen/Smol_Hex_Front_Skirt_43_Touch_Screen_Mount.stl

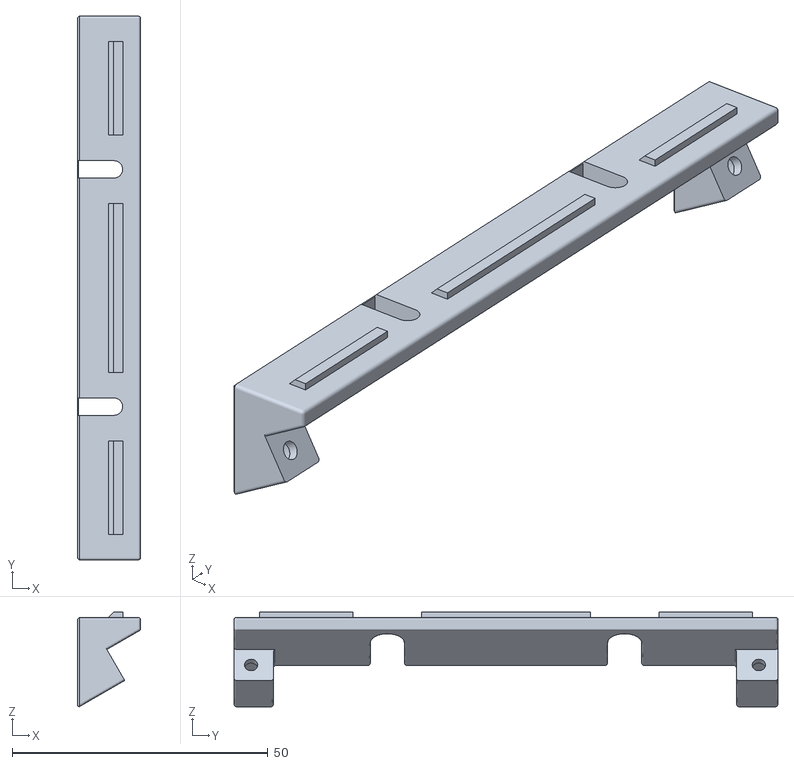
[picture p92: CAD file, 2023-08-23]
Micron+/Smol Hex Skirts/STLs/Front - 4.3 Touchscreen/Smol_Hex_Front_Skirt_43_Touch_Screen_Mount.stl
12.4 x 106.4 x 18.5
