Jadecky/Printer_Mods/Micron+/Smol Hex Skirts/STLs/Rear - Dual Keystone/(a)_Smol_Hex_Rear_Skirt_Dual_Keystone_Accent.stl

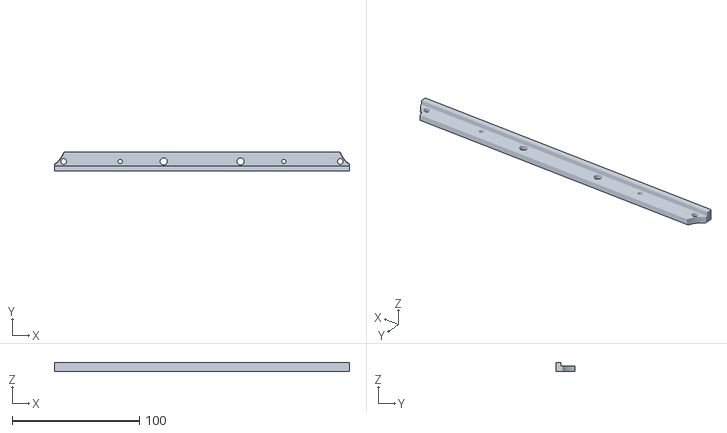
[picture p93: CAD file, 2023-08-23]
Micron+/Smol Hex Skirts/STLs/Rear - Dual Keystone/(a)_Smol_Hex_Rear_Skirt_Dual_Keystone_Accent.stl
231.6 x 15.0 x 7.25
