Jadecky/Printer_Mods/Micron+/Smol Hex Skirts/STLs/Stock/Smol_Hex_Rear_Skirt_Plain.stl

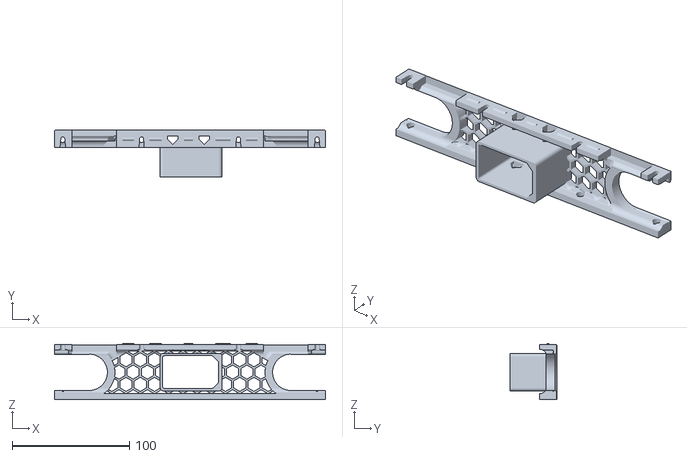
[picture p94: CAD file, 2023-08-23]
Micron+/Smol Hex Skirts/STLs/Stock/Smol_Hex_Rear_Skirt_Plain.stl
231.6 x 40.0 x 48.0
