Jadecky/Printer_Mods/Micron+/WAGO_221-415_1515_Mounts/Micron Electronics Bay (3mm Panel Clearance)/STLs/[a]_Micron_1515_3x_WAGO-221-415_mount.stl

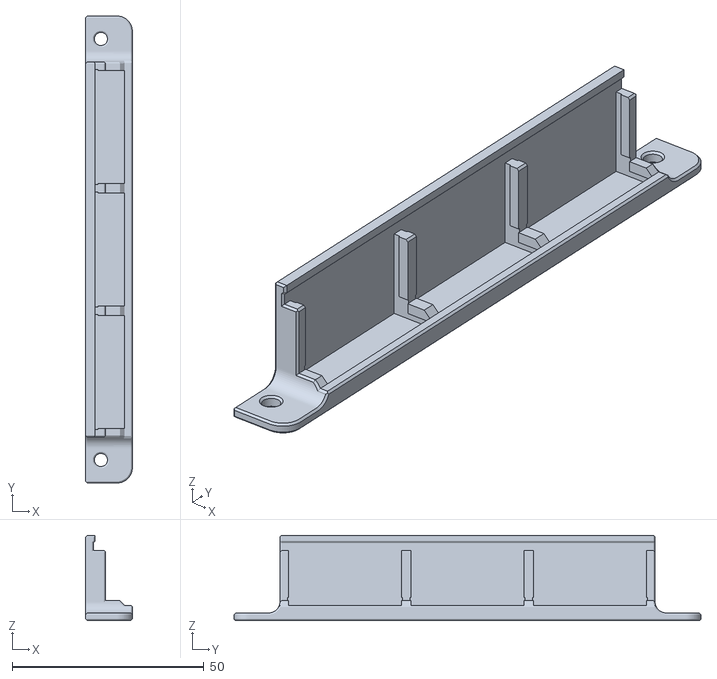
[picture p95: CAD file, 2024-08-17]
Micron+/WAGO_221-415_1515_Mounts/Micron Electronics Bay (3mm Panel Clearance)/STLs/[a]_Micron_1515_3x_WAGO-221-415_mount.stl
12.2 x 121.9 x 22.3
