Jadecky/Printer_Mods/Micron/Micron/AntHead_NH36 Mount/STLs/18mm Standoff/[a]_Spacer_L_18mmStandoff_x1.stl

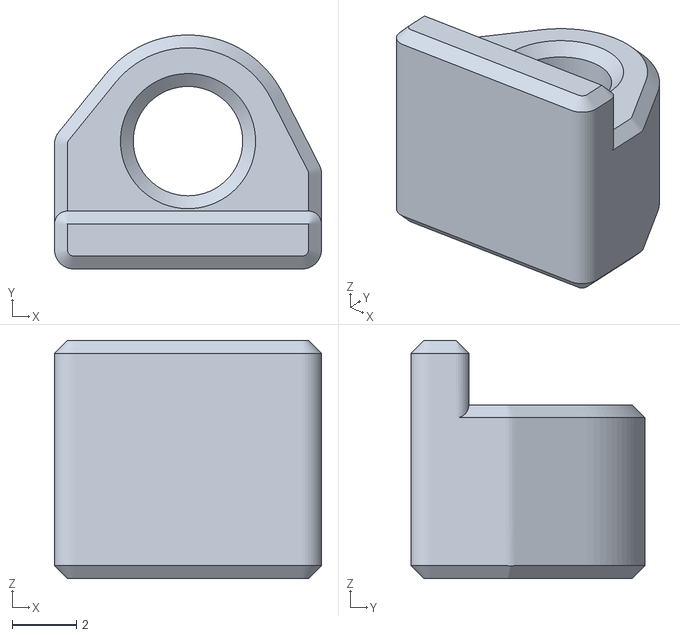
[picture p96: CAD file, 2025-10-04]
Micron/Micron/AntHead_NH36 Mount/STLs/18mm Standoff/[a]_Spacer_L_18mmStandoff_x1.stl
8.30 x 7.27 x 7.40
