Jadecky/Printer_Mods/Micron/Micron/AntHead_NH36 Mount/STLs/20mm Standoff/PUG_Mount_B_20mm_Standoff_x1.stl

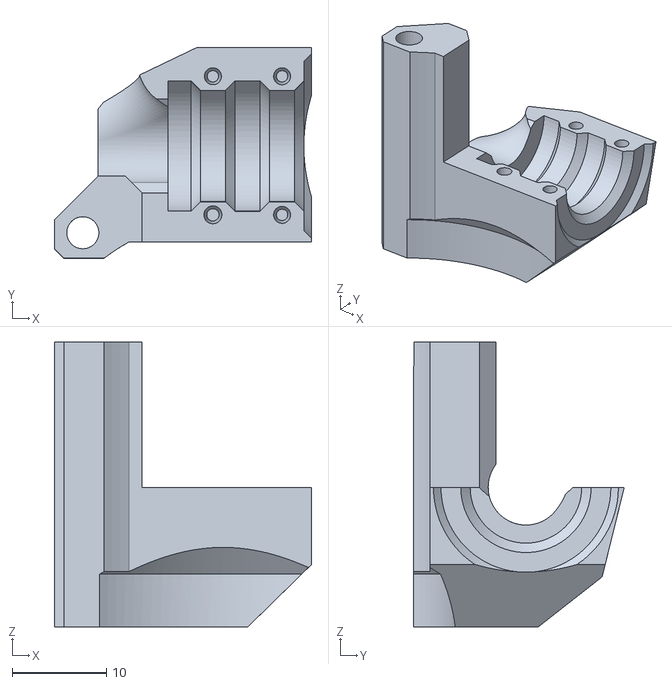
[picture p97: CAD file, 2025-10-04]
Micron/Micron/AntHead_NH36 Mount/STLs/20mm Standoff/PUG_Mount_B_20mm_Standoff_x1.stl
27.3 x 22.3 x 30.2
