Jadecky/Printer_Mods/Micron/Micron/AntHead_NH36 Mount/STLs/[a]_NH36_Mount_tabs_x1.stl

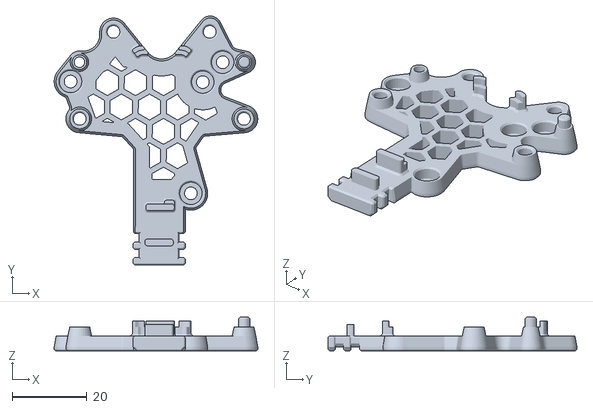
[picture p98: CAD file, 2025-10-04]
Micron/Micron/AntHead_NH36 Mount/STLs/[a]_NH36_Mount_tabs_x1.stl
54.4 x 66.5 x 9.00
