Jadecky/Printer_Mods/Micron/Micron/Display Bezel Border Accent/STLs/Bezel_accent_border_x1.stl

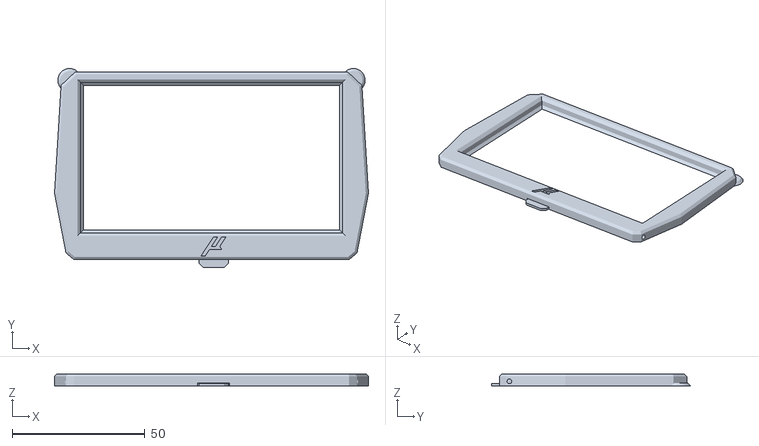
[picture p99: CAD file, 2025-07-15]
Micron/Micron/Display Bezel Border Accent/STLs/Bezel_accent_border_x1.stl
118.3 x 75.0 x 4.65
