Jadecky/Printer_Mods/Micron/Micron/ERCF 1515 Mount/STLs/ERCF_1515_Mount_1mm_Foam_x4.stl

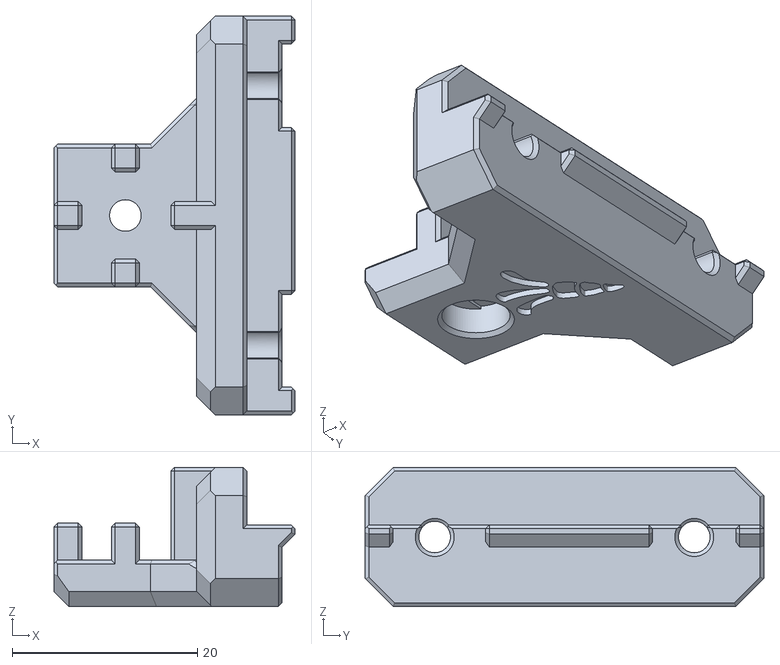
[picture p100: CAD file, 2024-08-23]
Micron/Micron/ERCF 1515 Mount/STLs/ERCF_1515_Mount_1mm_Foam_x4.stl
26.0 x 43.0 x 15.0
