Jadecky/Printer_Mods/Micron/Micron/Matchstick Mounts/STLs/Rainbow_Matchstick_Universal_Mount.stl

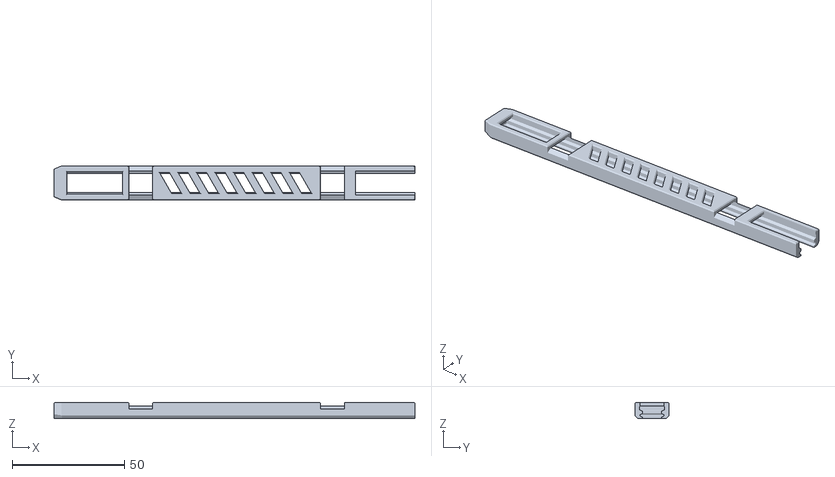
[picture p101: CAD file, 2023-12-18]
Micron/Micron/Matchstick Mounts/STLs/Rainbow_Matchstick_Universal_Mount.stl
161.0 x 15.2 x 7.30
