Jadecky/Printer_Mods/Micron/Micron/Micron Bed Stand Off Sleeves/STLs/[a]_Micron_Bed_Stand_Off_Sleeve_Blank.stl

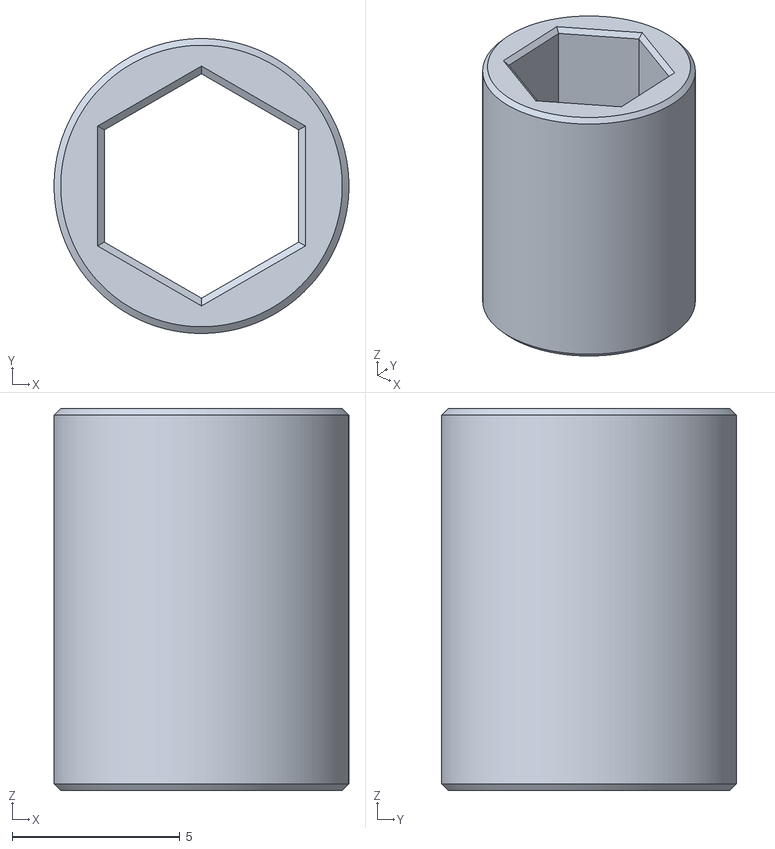
[picture p102: CAD file, 2024-08-17]
Micron/Micron/Micron Bed Stand Off Sleeves/STLs/[a]_Micron_Bed_Stand_Off_Sleeve_Blank.stl
8.80 x 8.80 x 11.4
