Jadecky/Printer_Mods/Micron/Micron/Micron+ Bambu Nozzle Scubber_with Purge Bucket/STLs/Brush on Left/[a]_Bucket_L_x1.stl

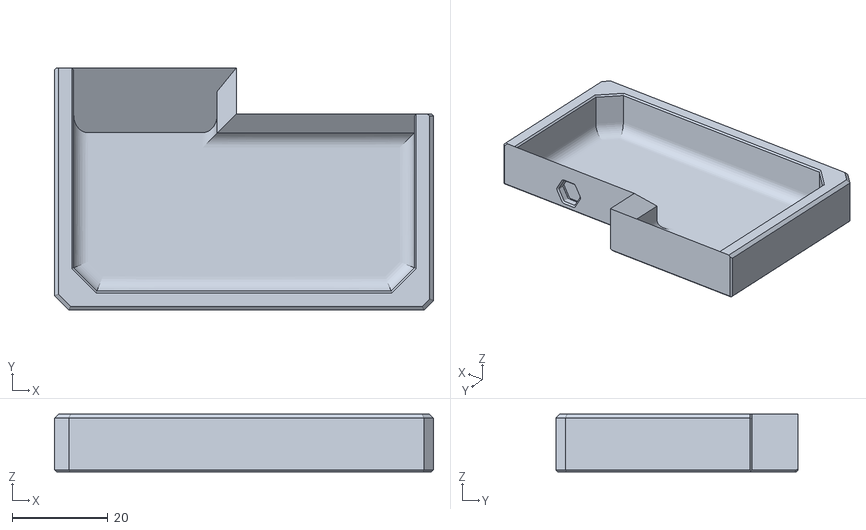
[picture p103: CAD file, 2025-11-23]
Micron/Micron/Micron+ Bambu Nozzle Scubber_with Purge Bucket/STLs/Brush on Left/[a]_Bucket_L_x1.stl
79.0 x 50.5 x 12.0
