Jadecky/Printer_Mods/Micron/Micron/Micron+ Bambu Nozzle Scubber_with Purge Bucket/STLs/Brush on Right/Brush_Holder_LDO_Kit_x1.stl

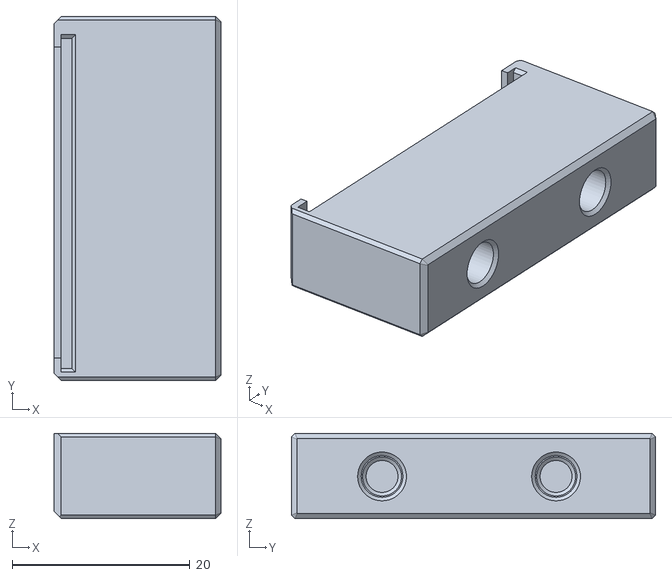
[picture p104: CAD file, 2025-11-23]
Micron/Micron/Micron+ Bambu Nozzle Scubber_with Purge Bucket/STLs/Brush on Right/Brush_Holder_LDO_Kit_x1.stl
18.8 x 41.0 x 9.60
