Jadecky/Printer_Mods/Micron/Micron/Stealth Fan Grills/STLs/Fan_Grill_x2.stl

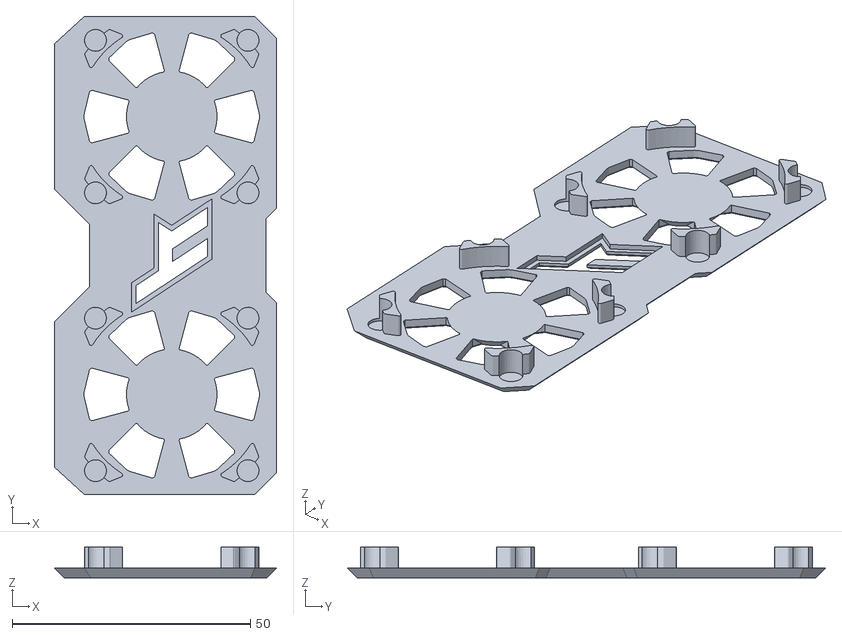
[picture p106: CAD file, 2025-06-29]
Micron/Micron/Stealth Fan Grills/STLs/Fan_Grill_x2.stl
46.6 x 100.3 x 6.40
