Jadecky/Printer_Mods/Misc Items/Bed Aux Umbilical/CAD/Micron_Bed_Aux_Umbilical_Mount.step

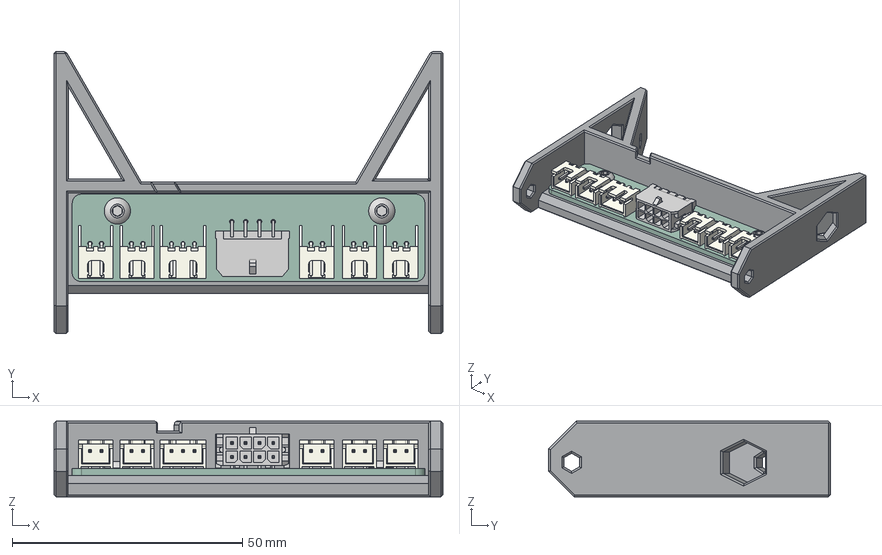
[picture p107: CAD file, 2025-11-23]
Misc Items/Bed Aux Umbilical/CAD/Micron_Bed_Aux_Umbilical_Mount.step
84.5 x 61.2 x 16.4 mm
Wago Mount 413
M3x6 BHCS x 2
JST_XH_S2B-XH-A-1_1x02_P2.50mm_Horizontal x 5
JST_XH_S3B-XH-A-1_1x03_P2.50mm_Horizontal
Bed_Aux_Umbiical_PCB_PCB
