Jadecky/Printer_Mods/Micron+/MDC/STLs/Heatset Version/Drill Guides/Drill_Guide_TL_1mm.stl

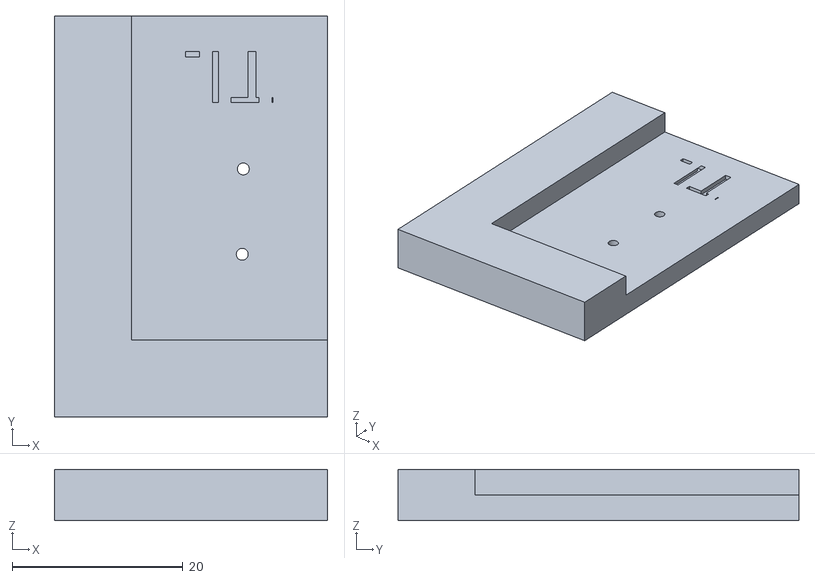
[picture p108: CAD file, 2023-09-10]
Micron+/MDC/STLs/Heatset Version/Drill Guides/Drill_Guide_TL_1mm.stl
32.0 x 47.0 x 6.00
