Jadecky/Printer_Mods/Micron+/MDC/STLs/Heatset Version/Hinge_Frame_Mount_x2.stl

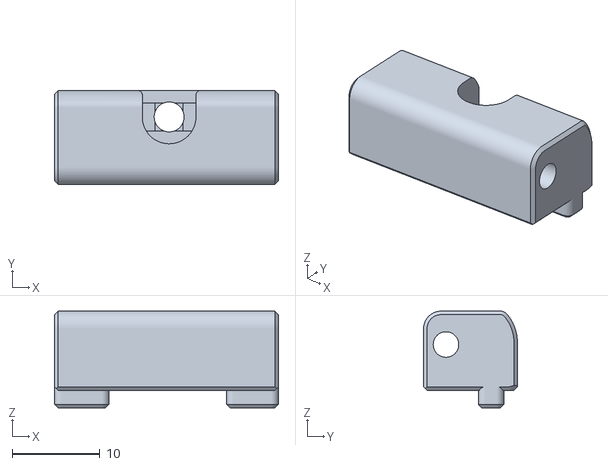
[picture p109: CAD file, 2023-09-10]
Micron+/MDC/STLs/Heatset Version/Hinge_Frame_Mount_x2.stl
25.5 x 10.7 x 11.0
