Jadecky/Printer_Mods/Micron+/Smol Hex Skirts/STLs/Front - 4.3 Touchscreen/Smol_Hex_Front_Skirt_43_Touch_Screen_R.stl

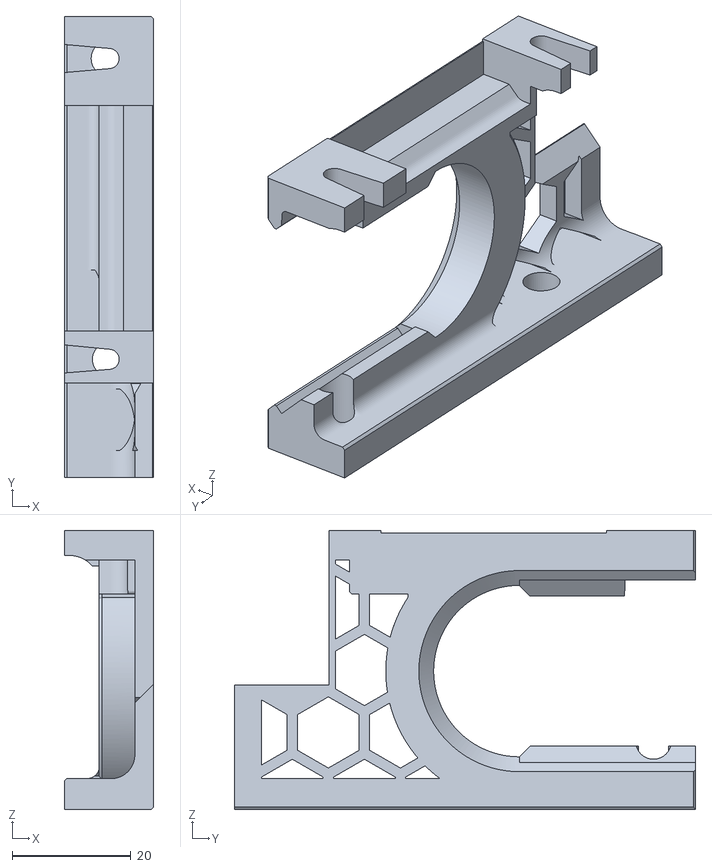
[picture p110: CAD file, 2023-08-23]
Micron+/Smol Hex Skirts/STLs/Front - 4.3 Touchscreen/Smol_Hex_Front_Skirt_43_Touch_Screen_R.stl
15.0 x 77.7 x 47.0
