Jadecky/Printer_Mods/Micron+/Smol Hex Skirts/STLs/Stock/Smol_Hex_Sideskirt_A_x2.stl

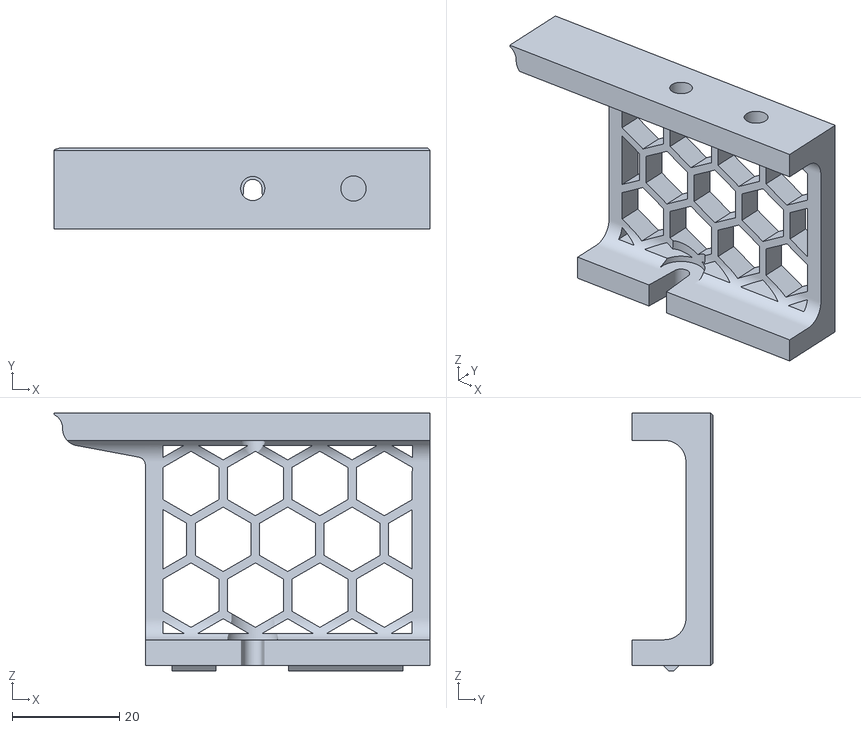
[picture p111: CAD file, 2023-08-23]
Micron+/Smol Hex Skirts/STLs/Stock/Smol_Hex_Sideskirt_A_x2.stl
70.0 x 15.0 x 48.0
