Jadecky/Printer_Mods/Micron/Micron/AntHead_NH36 Mount/STLs/18mm Standoff/PUG_Mount_B_18mm_Standoff_x1.stl

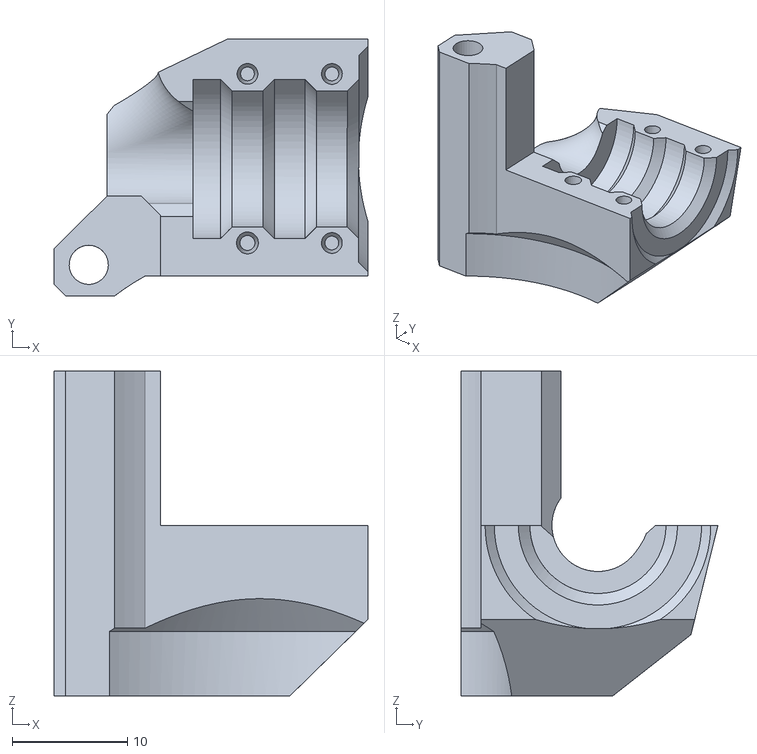
[picture p112: CAD file, 2025-10-04]
Micron/Micron/AntHead_NH36 Mount/STLs/18mm Standoff/PUG_Mount_B_18mm_Standoff_x1.stl
27.3 x 22.3 x 28.2
