Jadecky/Printer_Mods/Micron/Micron/Micron+ Bambu Nozzle Scubber_with Purge Bucket/STLs/Brush on Left/Base_Stock_L_x1.stl

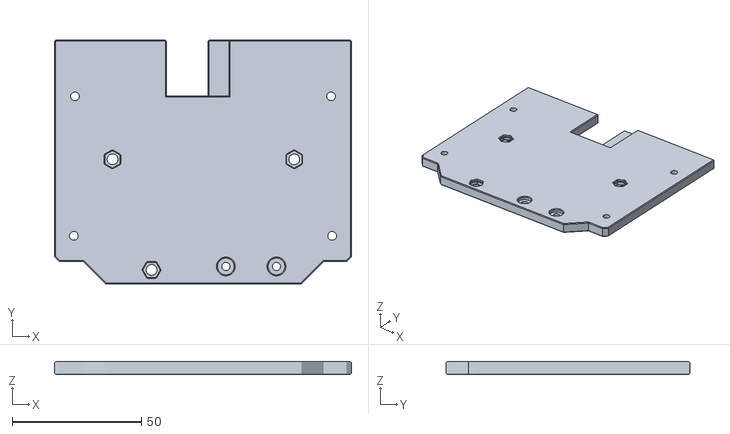
[picture p114: CAD file, 2025-11-23]
Micron/Micron/Micron+ Bambu Nozzle Scubber_with Purge Bucket/STLs/Brush on Left/Base_Stock_L_x1.stl
115.0 x 94.4 x 5.00
