Jadecky/Printer_Mods/Micron/Micron/Micron+ Bambu Nozzle Scubber_with Purge Bucket/STLs/Brush on Right/Base_no_chain_x1.stl

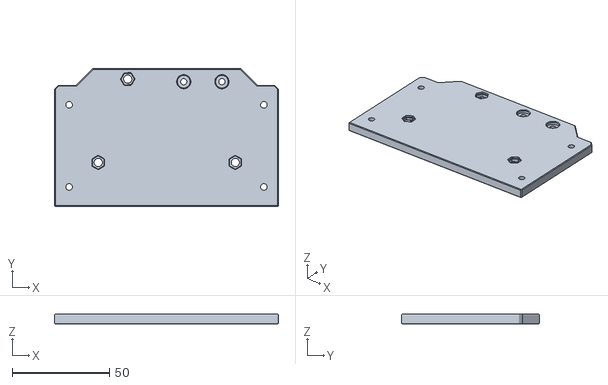
[picture p115: CAD file, 2025-06-16]
Micron/Micron/Micron+ Bambu Nozzle Scubber_with Purge Bucket/STLs/Brush on Right/Base_no_chain_x1.stl
115.0 x 70.8 x 5.00
