Jadecky/Printer_Mods/Micron+/MDC/STLs/Heatset Version/Bottom_Hinge_Door_Mount.stl

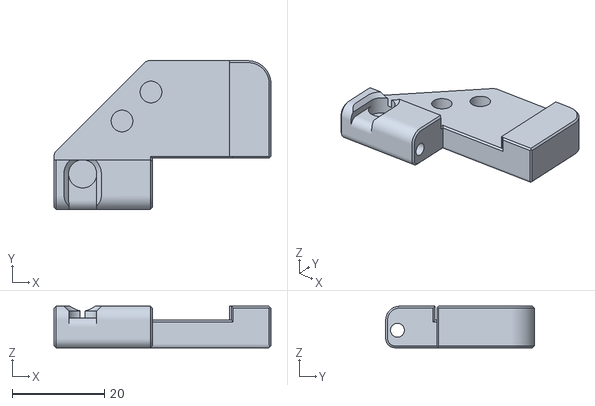
[picture p117: CAD file, 2023-09-10]
Micron+/MDC/STLs/Heatset Version/Bottom_Hinge_Door_Mount.stl
47.0 x 32.2 x 9.00
