Jadecky/Printer_Mods/Micron+/MDC/STLs/Heatset Version/Drill Guides/Drill_Guide_BL.stl

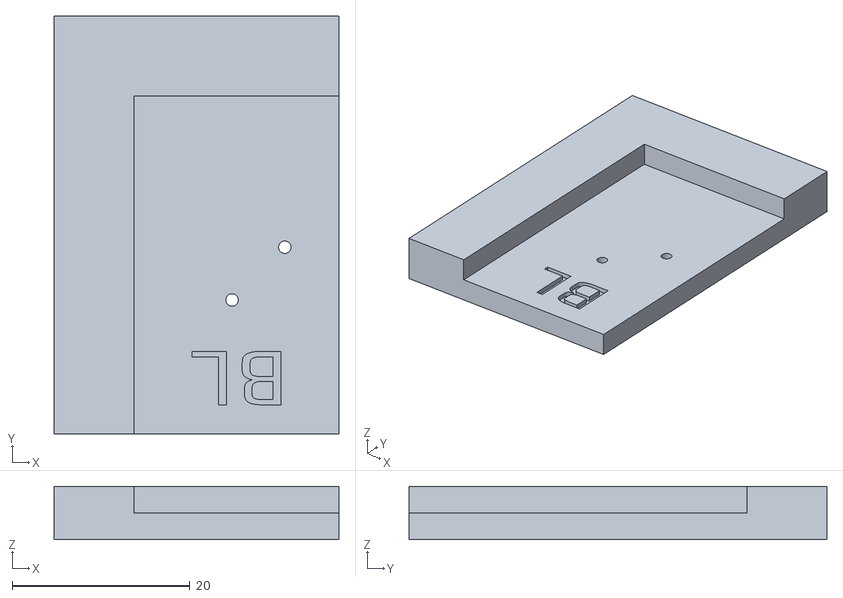
[picture p118: CAD file, 2023-09-10]
Micron+/MDC/STLs/Heatset Version/Drill Guides/Drill_Guide_BL.stl
32.0 x 47.0 x 6.00
