Jadecky/Printer_Mods/Micron+/MDC/STLs/VHB Tape Version/VHB_Top_Left_Corner.stl

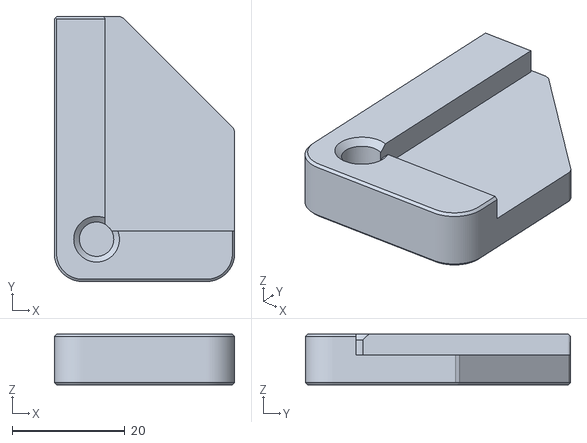
[picture p119: CAD file, 2023-09-10]
Micron+/MDC/STLs/VHB Tape Version/VHB_Top_Left_Corner.stl
32.0 x 47.0 x 9.00
