Jadecky/Printer_Mods/Micron+/Smol Hex Skirts/STLs/Front - 3.5 Touchscreen/(a)_Smol_Hex_Front_Skirt_35_Touch_Screen_Faceplate.stl

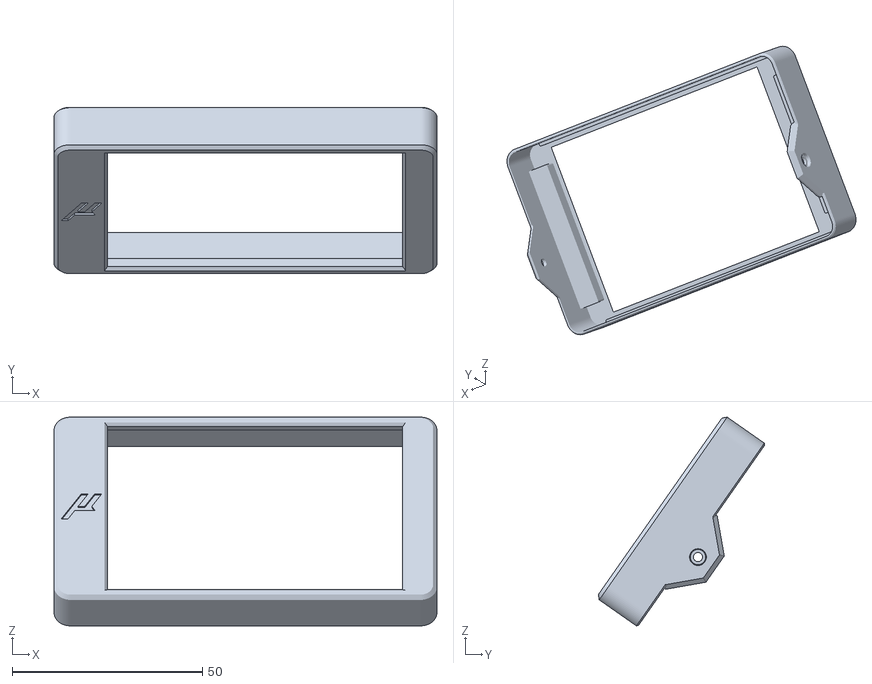
[picture p120: CAD file, 2023-08-23]
Micron+/Smol Hex Skirts/STLs/Front - 3.5 Touchscreen/(a)_Smol_Hex_Front_Skirt_35_Touch_Screen_Faceplate.stl
100.6 x 43.7 x 54.8
