Jadecky/Printer_Mods/Micron/Micron/AntHead_NH36 Mount/STLs/18mm Standoff/PUG_Mount_A_18mm_Standoff_x1.stl

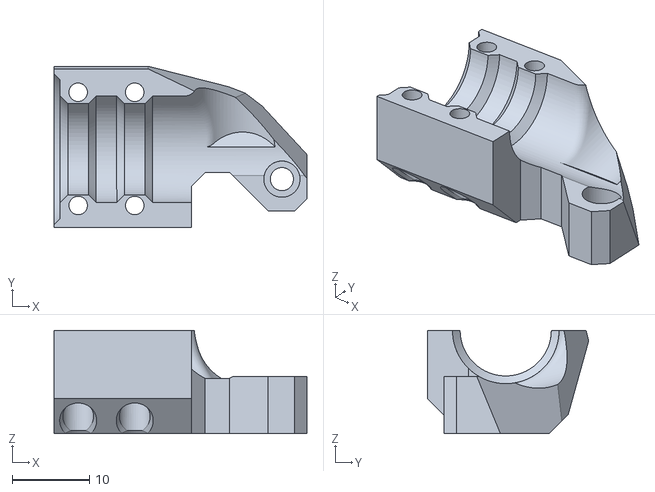
[picture p122: CAD file, 2025-10-04]
Micron/Micron/AntHead_NH36 Mount/STLs/18mm Standoff/PUG_Mount_A_18mm_Standoff_x1.stl
32.8 x 20.9 x 13.4
