Jadecky/Printer_Mods/Micron/Micron/AntHead_NH36 Mount/STLs/20mm Standoff/PUG_Mount_A_20mm_Standoff_x1.stl

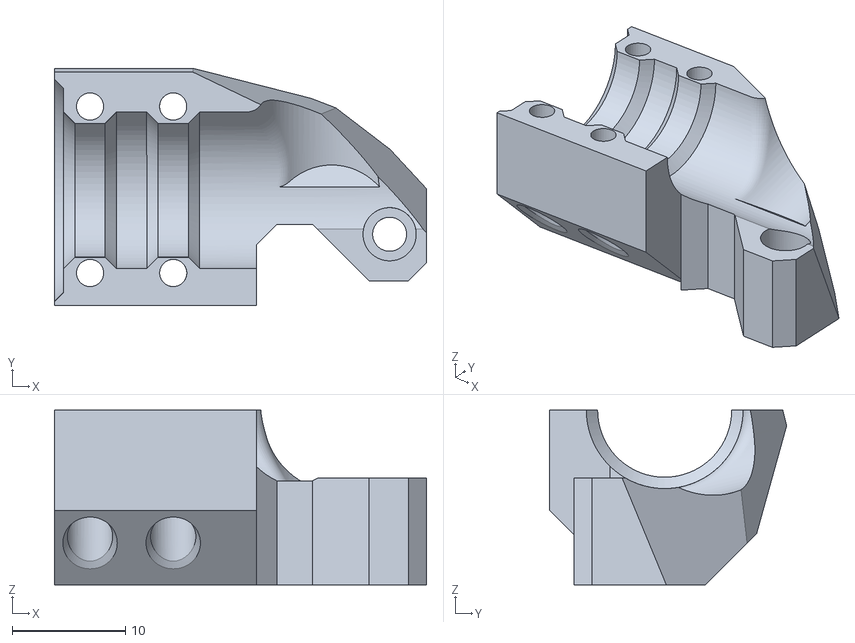
[picture p123: CAD file, 2025-10-04]
Micron/Micron/AntHead_NH36 Mount/STLs/20mm Standoff/PUG_Mount_A_20mm_Standoff_x1.stl
32.8 x 20.9 x 15.4
