Jadecky/Printer_Mods/Micron/Micron/Micron+ Bambu Nozzle Scubber_with Purge Bucket/STLs/Brush on Right/Base_boop_x1.stl

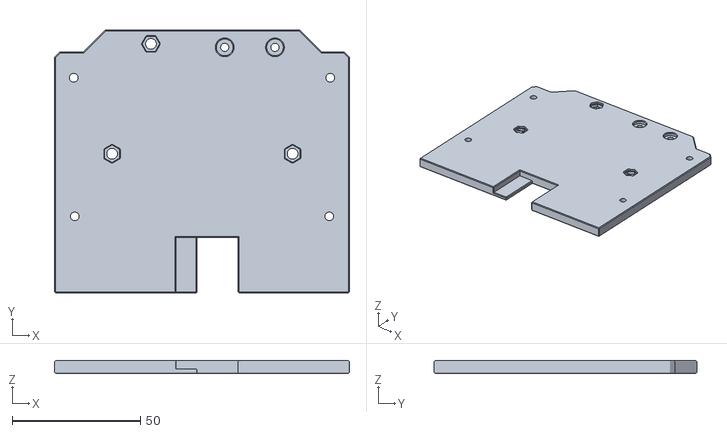
[picture p124: CAD file, 2025-06-16]
Micron/Micron/Micron+ Bambu Nozzle Scubber_with Purge Bucket/STLs/Brush on Right/Base_boop_x1.stl
115.0 x 102.5 x 5.00
