Jadecky/Printer_Mods/Micron/Micron/Micron_NEMA17/STLs/Pinned/A_Drive_Frame_Upper_Pinned_x1.stl

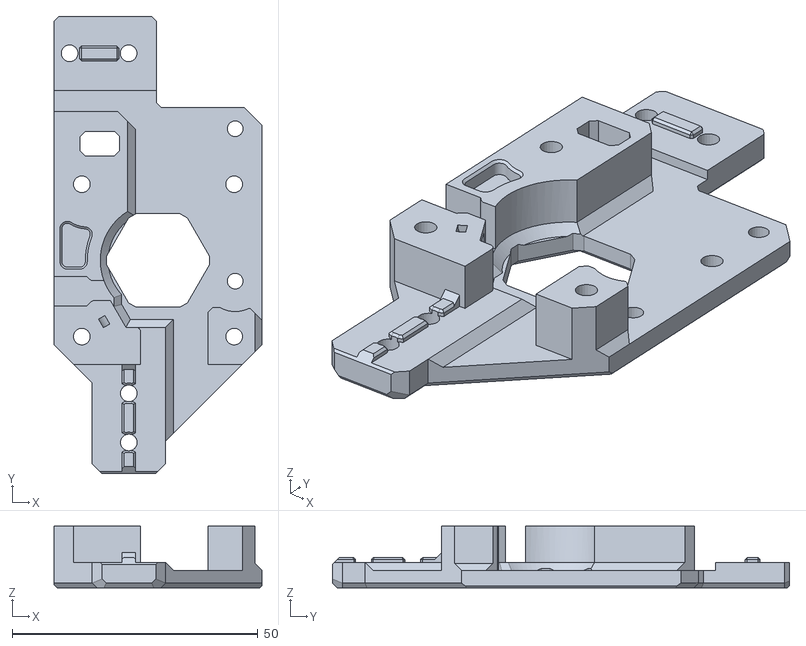
[picture p125: CAD file, 2025-10-28]
Micron/Micron/Micron_NEMA17/STLs/Pinned/A_Drive_Frame_Upper_Pinned_x1.stl
42.3 x 93.0 x 12.6
