Jadecky/Printer_Mods/Micron+/MDC/STLs/Heatset Version/Drill Guides/Drill_Guide_BR.stl

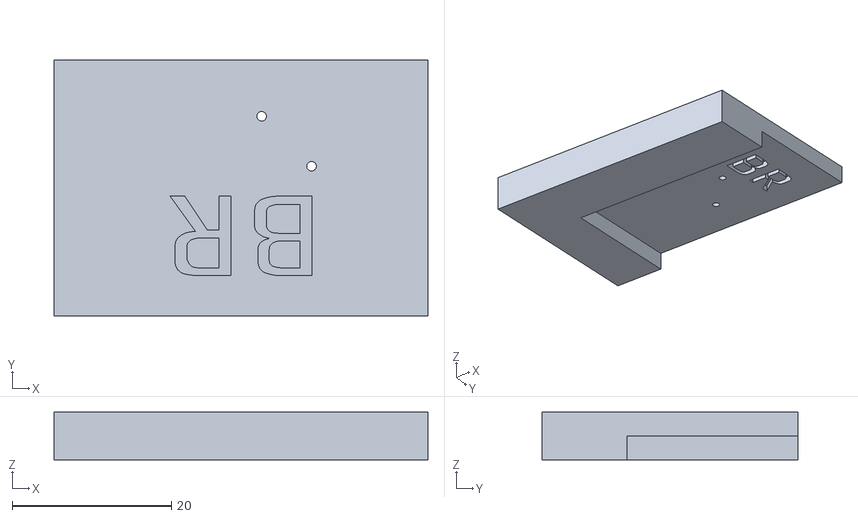
[picture p126: CAD file, 2023-09-10]
Micron+/MDC/STLs/Heatset Version/Drill Guides/Drill_Guide_BR.stl
47.0 x 32.2 x 6.00
