Jadecky/Printer_Mods/Micron+/MDC/STLs/VHB Tape Version/VHB_Bottom_Hinge_Door_Mount.stl

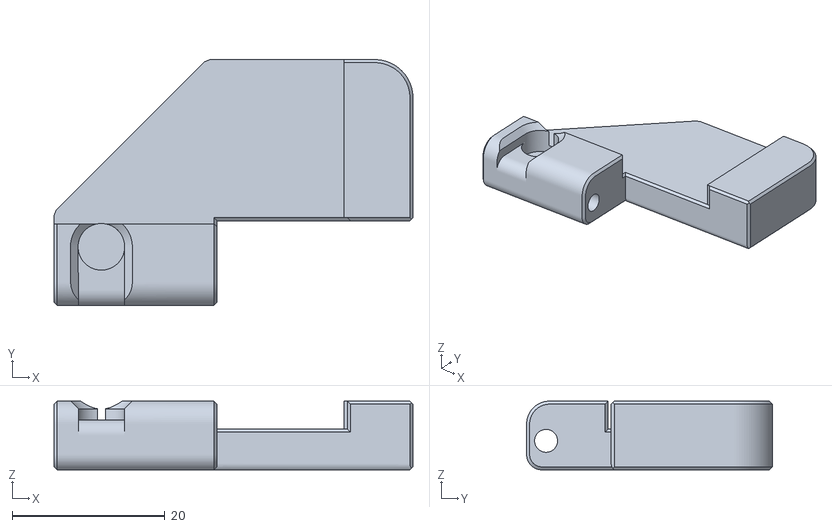
[picture p127: CAD file, 2023-09-10]
Micron+/MDC/STLs/VHB Tape Version/VHB_Bottom_Hinge_Door_Mount.stl
47.0 x 32.2 x 9.00
