Jadecky/Printer_Mods/Micron+/MDC/STLs/Heatset Version/Top_Hinge_Door_Mount_MMU.stl

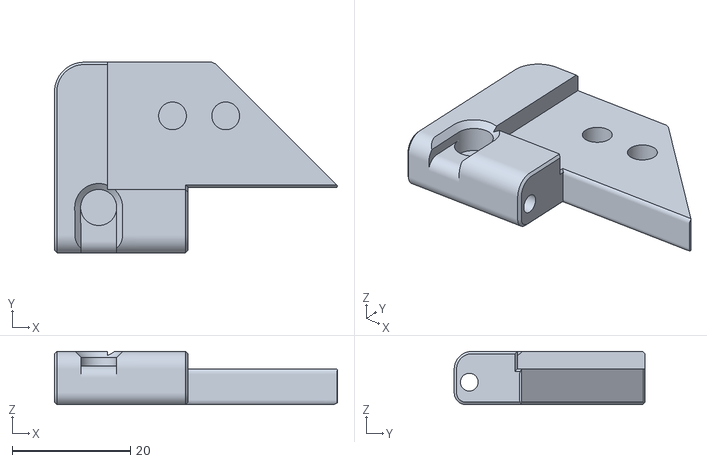
[picture p128: CAD file, 2023-09-10]
Micron+/MDC/STLs/Heatset Version/Top_Hinge_Door_Mount_MMU.stl
47.9 x 32.2 x 9.00
