Jadecky/Printer_Mods/Micron/Micron/Micron+ Bambu Nozzle Scubber_with Purge Bucket/STLs/Brush on Left/Brush_holder_L_x1.stl

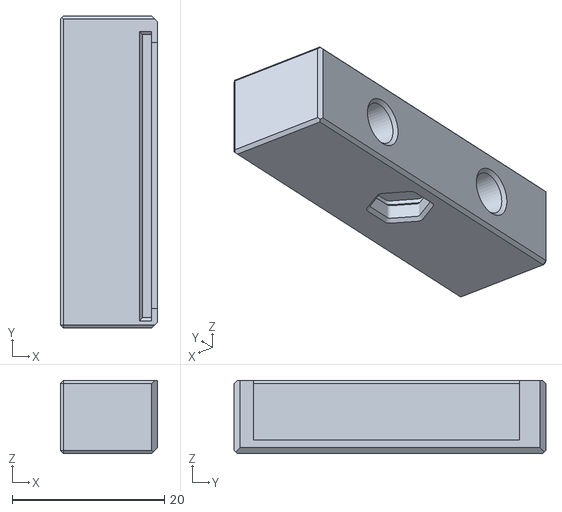
[picture p129: CAD file, 2025-11-23]
Micron/Micron/Micron+ Bambu Nozzle Scubber_with Purge Bucket/STLs/Brush on Left/Brush_holder_L_x1.stl
12.8 x 41.0 x 9.60
