Jadecky/Printer_Mods/Micron+/MDC/STLs/Heatset Version/Bottom_Left_Door_Corner.stl

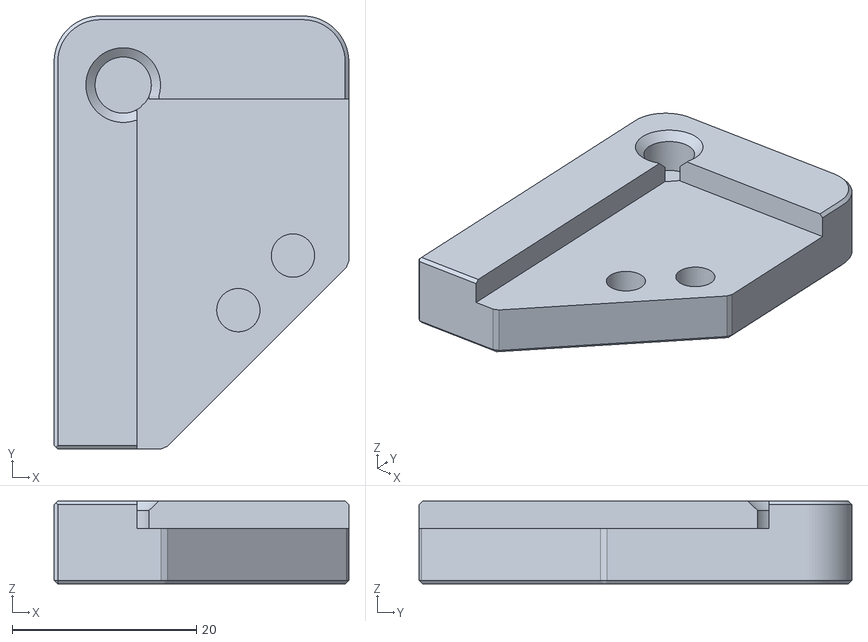
[picture p130: CAD file, 2023-09-10]
Micron+/MDC/STLs/Heatset Version/Bottom_Left_Door_Corner.stl
32.0 x 47.0 x 9.00
